KPU-RISC/KPU/Eagle/3. Instruction Decoder/04_ALU.brd

## EAGLE design Eagle/3. Instruction Decoder/04_ALU.brd (2017-04-16)

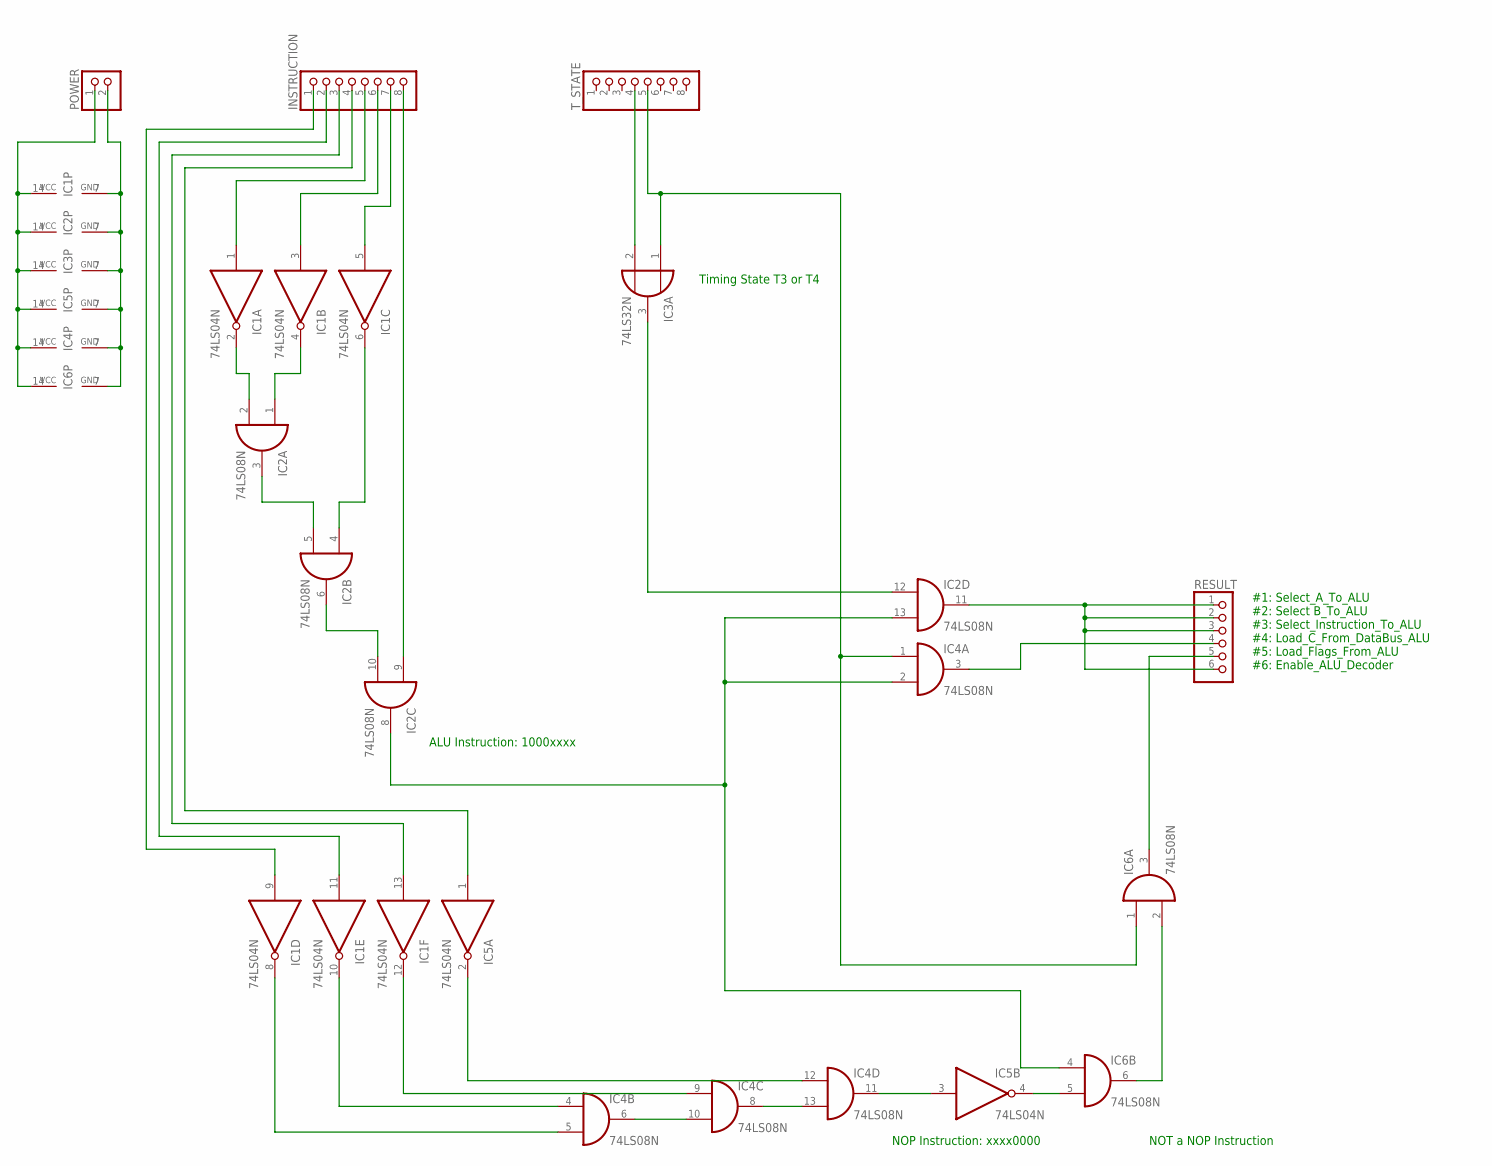
[picture p17: schematic 04_ALU.sch]

Parts:
IC1, IC5: 74LS04N; DIL14
IC2, IC4, IC6: 74LS08N; DIL14
IC3: 74LS32N; DIL14
INSTRUCTION: PINHD-1X8; 1X08
POWER: PINHD-1X2; 1X02
RESULT: PINHD-1X6; 1X06
T_STATE: PINHD-1X8; 1X08

Connections:
GND: IC1.7 (GND), IC2.7 (GND), IC3.7 (GND), IC4.7 (GND), IC5.7 (GND), IC6.7 (GND), POWER.2
unnamed: IC1.1 (I), INSTRUCTION.5
unnamed: IC1.3 (I), INSTRUCTION.6
unnamed: IC1.5 (I), INSTRUCTION.7
unnamed: IC1.2 (O), IC2.2 (I1)
unnamed: IC1.4 (O), IC2.1 (I0)
unnamed: IC2.3 (O), IC2.5 (I1)
unnamed: IC1.6 (O), IC2.4 (I0)
unnamed: IC2.9 (I0), INSTRUCTION.8
unnamed: IC2.6 (O), IC2.10 (I1)
unnamed: IC3.2 (I1), T_STATE.4
unnamed: IC3.1 (I0), IC4.1 (I0), IC6.1 (I0), T_STATE.5
unnamed: IC2.8 (O), IC2.13 (I1), IC4.2 (I1), IC6.4 (I0)
unnamed: IC2.12 (I0), IC3.3 (O)
unnamed: IC2.11 (O), RESULT.1, RESULT.2, RESULT.3, RESULT.6
unnamed: IC4.3 (O), RESULT.4
unnamed: IC1.9 (I), INSTRUCTION.1
unnamed: IC1.11 (I), INSTRUCTION.2
unnamed: IC1.13 (I), INSTRUCTION.3
unnamed: IC5.1 (I), INSTRUCTION.4
unnamed: IC1.8 (O), IC4.5 (I1)
unnamed: IC1.10 (O), IC4.4 (I0)
unnamed: IC4.6 (O), IC4.10 (I1)
unnamed: IC1.12 (O), IC4.9 (I0)
unnamed: IC4.8 (O), IC4.13 (I1)
unnamed: IC4.12 (I0), IC5.2 (O)
unnamed: IC4.11 (O), IC5.3 (I)
unnamed: IC5.4 (O), IC6.5 (I1)
unnamed: IC6.3 (O), RESULT.5
unnamed: IC6.2 (I1), IC6.6 (O)
VCC: IC1.14 (VCC), IC2.14 (VCC), IC3.14 (VCC), IC4.14 (VCC), IC5.14 (VCC), IC6.14 (VCC), POWER.1

Notes on the sheet:
ALU Instruction: 1000xxxx
Timing State T3 or T4
#1: Select_A_To_ALU #2: Select B_To_ALU #3: Select_Instruction_To_ALU #4: Load_C_From_DataBus_ALU #5: Load_Flags_From_ALU #6: Enable_ALU_Decoder
NOP Instruction: xxxx0000
NOT a NOP Instruction

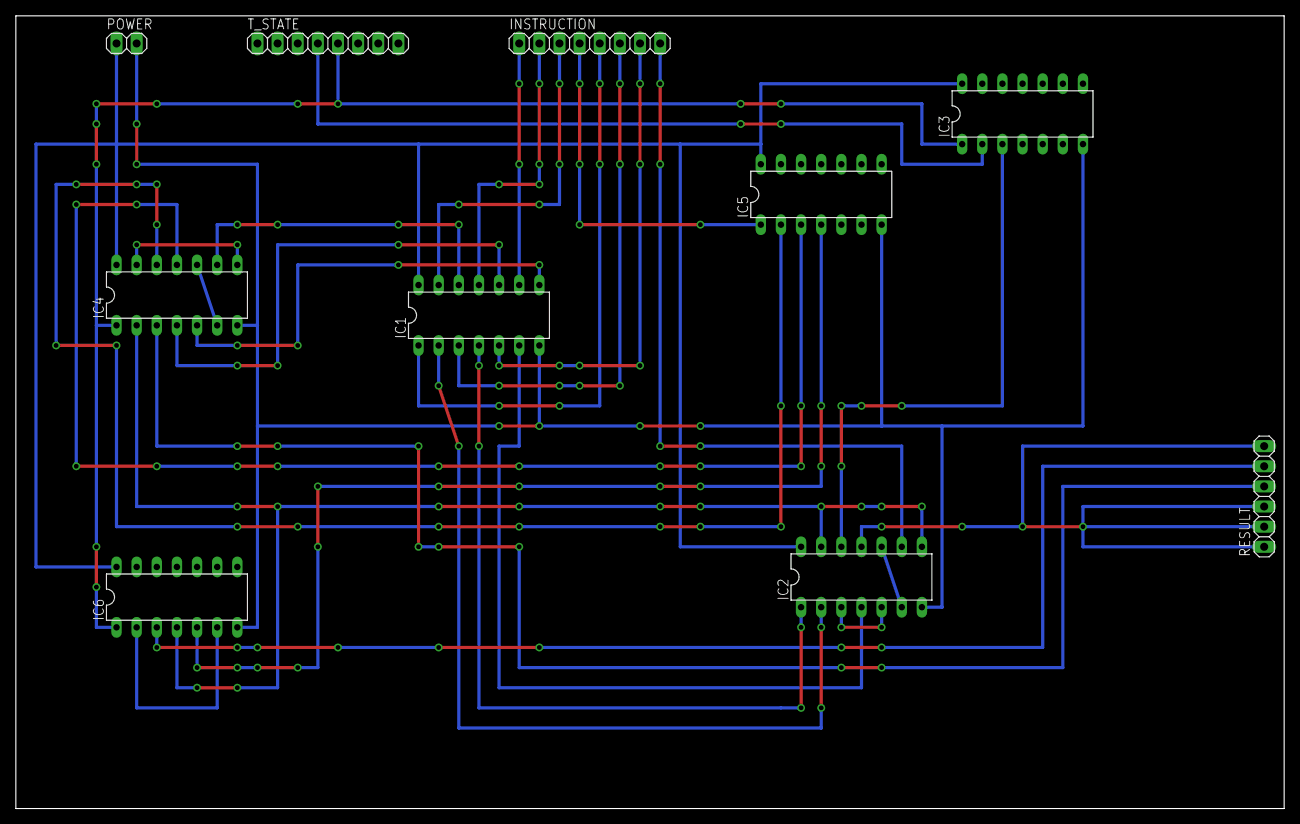
[picture p18: board 04_ALU.brd from above]

Board: 2 copper layers, 160.0 x 100.0 mm, 10 parts (0 on the bottom side), 31 nets.
