KPU-RISC/KPU/Eagle/3. Instruction Decoder/13_RESTOREFLAGS.brd

## EAGLE design Eagle/3. Instruction Decoder/13_RESTOREFLAGS.brd (2017-04-16)

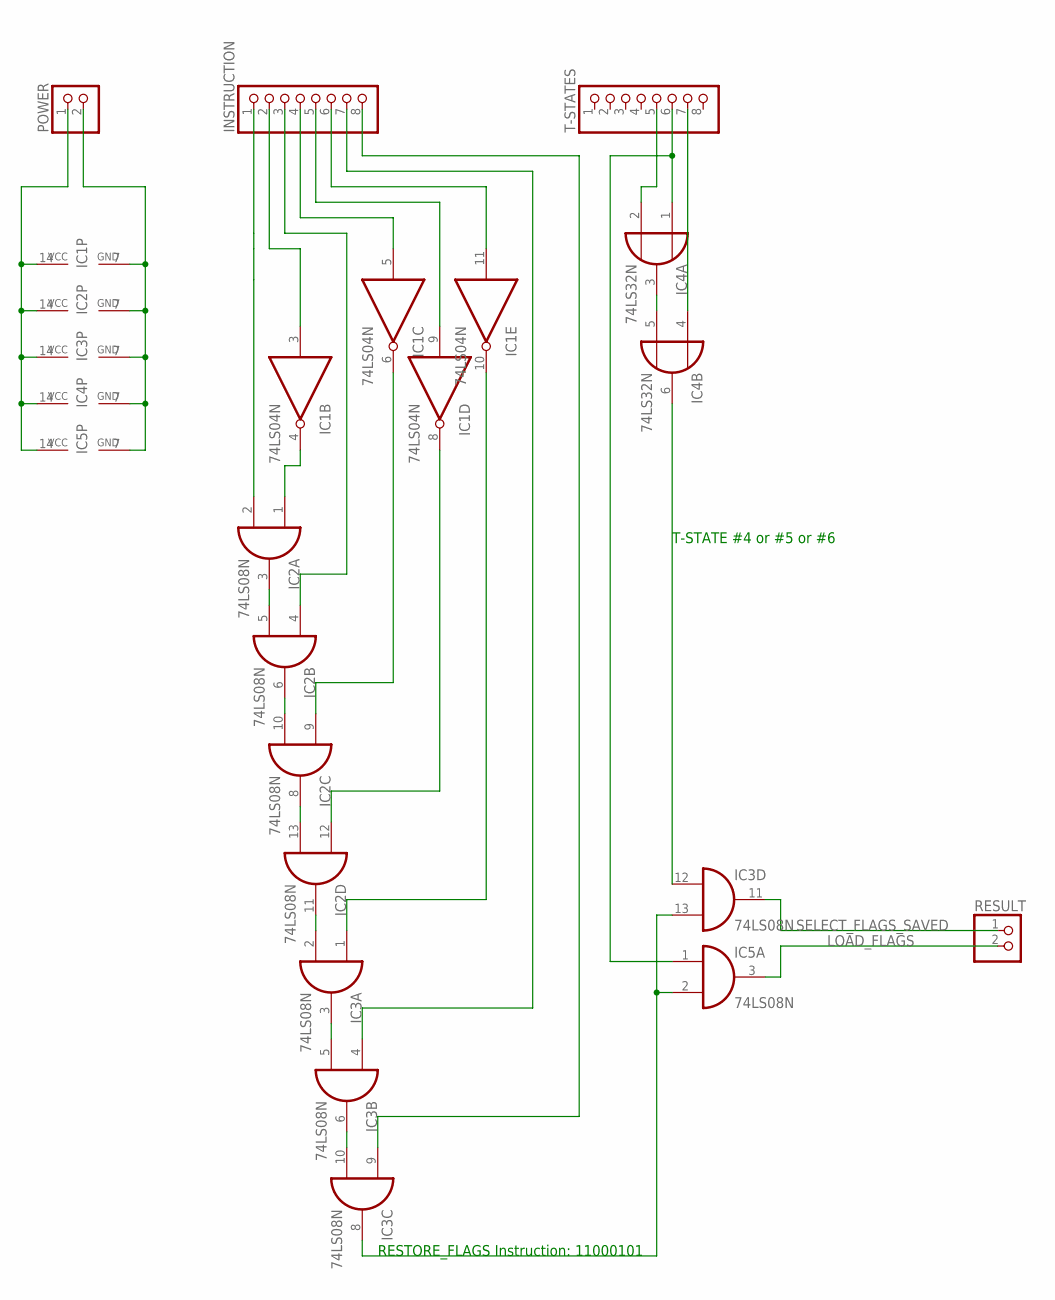
[picture p19: schematic 13_RESTOREFLAGS.sch]

Parts:
IC1: 74LS04N; DIL14
IC2, IC3, IC5: 74LS08N; DIL14
IC4: 74LS32N; DIL14
INSTRUCTION: PINHD-1X8; 1X08
POWER: PINHD-1X2; 1X02
RESULT: PINHD-1X2; 1X02
T-STATES: PINHD-1X8; 1X08

Connections:
GND: IC1.7 (GND), IC2.7 (GND), IC3.7 (GND), IC4.7 (GND), IC5.7 (GND), POWER.2
LOAD_FLAGS: IC5.3 (O), RESULT.2
unnamed: IC2.2 (I1), INSTRUCTION.1
unnamed: IC1.3 (I), INSTRUCTION.2
unnamed: IC2.4 (I0), INSTRUCTION.3
unnamed: IC4.3 (O), IC4.5 (I1)
unnamed: IC1.4 (O), IC2.1 (I0)
unnamed: IC1.6 (O), IC2.9 (I0)
unnamed: IC1.8 (O), IC2.12 (I0)
unnamed: IC1.10 (O), IC3.1 (I0)
unnamed: IC1.5 (I), INSTRUCTION.4
unnamed: IC1.9 (I), INSTRUCTION.5
unnamed: IC1.11 (I), INSTRUCTION.6
unnamed: IC3.4 (I0), INSTRUCTION.7
unnamed: IC3.9 (I0), INSTRUCTION.8
unnamed: IC4.4 (I0), T-STATES.7
unnamed: IC2.3 (O), IC2.5 (I1)
unnamed: IC2.6 (O), IC2.10 (I1)
unnamed: IC2.8 (O), IC2.13 (I1)
unnamed: IC2.11 (O), IC3.2 (I1)
unnamed: IC3.3 (O), IC3.5 (I1)
unnamed: IC3.6 (O), IC3.10 (I1)
unnamed: IC3.8 (O), IC3.13 (I1), IC5.2 (I1)
unnamed: IC4.1 (I0), IC5.1 (I0), T-STATES.6
unnamed: IC3.12 (I0), IC4.6 (O)
unnamed: IC4.2 (I1), T-STATES.5
SELECT_FLAGS_SAVED: IC3.11 (O), RESULT.1
VCC: IC1.14 (VCC), IC2.14 (VCC), IC3.14 (VCC), IC4.14 (VCC), IC5.14 (VCC), POWER.1

Notes on the sheet:
RESTORE_FLAGS Instruction: 11000101
T-STATE #4 or #5 or #6

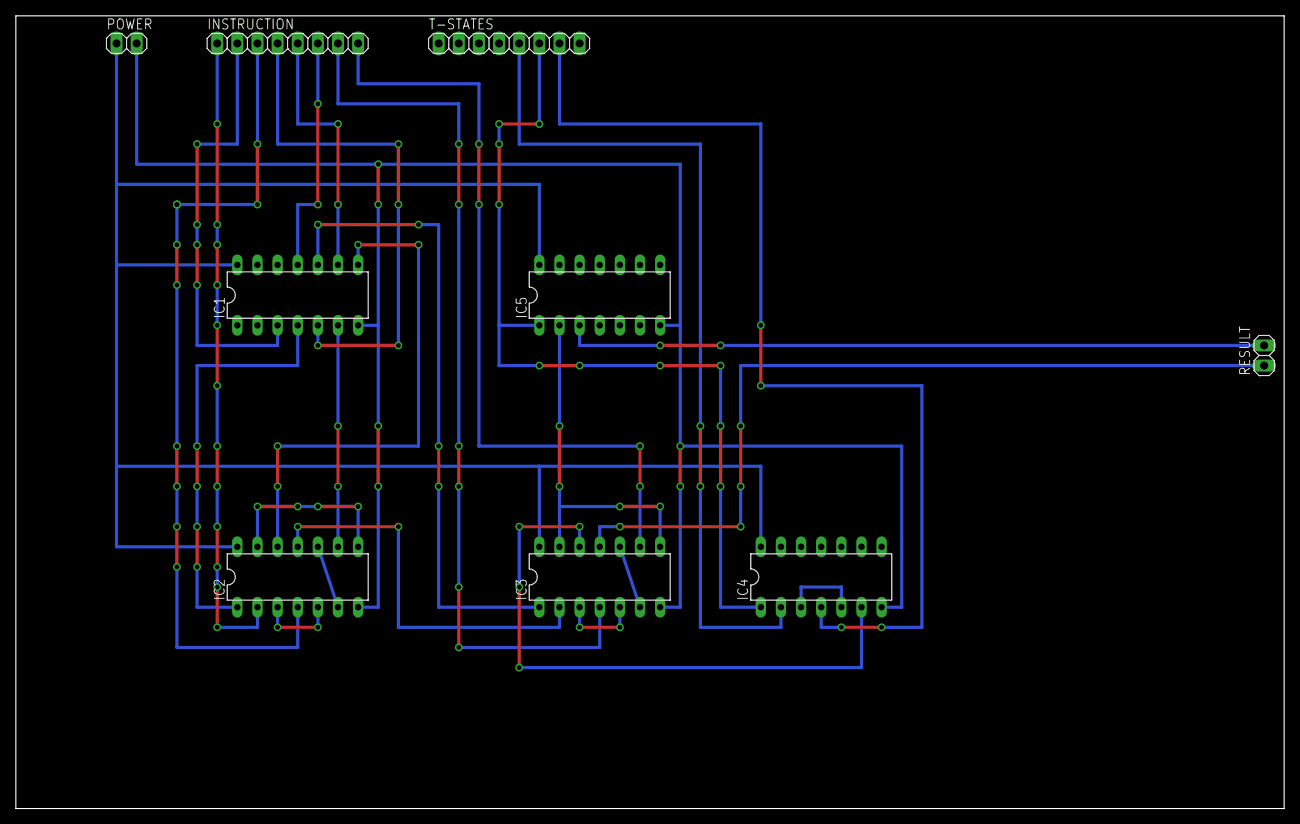
[picture p20: board 13_RESTOREFLAGS.brd from above]

Board: 2 copper layers, 160.0 x 100.0 mm, 9 parts (0 on the bottom side), 28 nets.
