KPU-RISC/KPU/Eagle/1. General/ControlLineSelector.brd

## EAGLE design Eagle/1. General/ControlLineSelector.brd (2017-04-16)

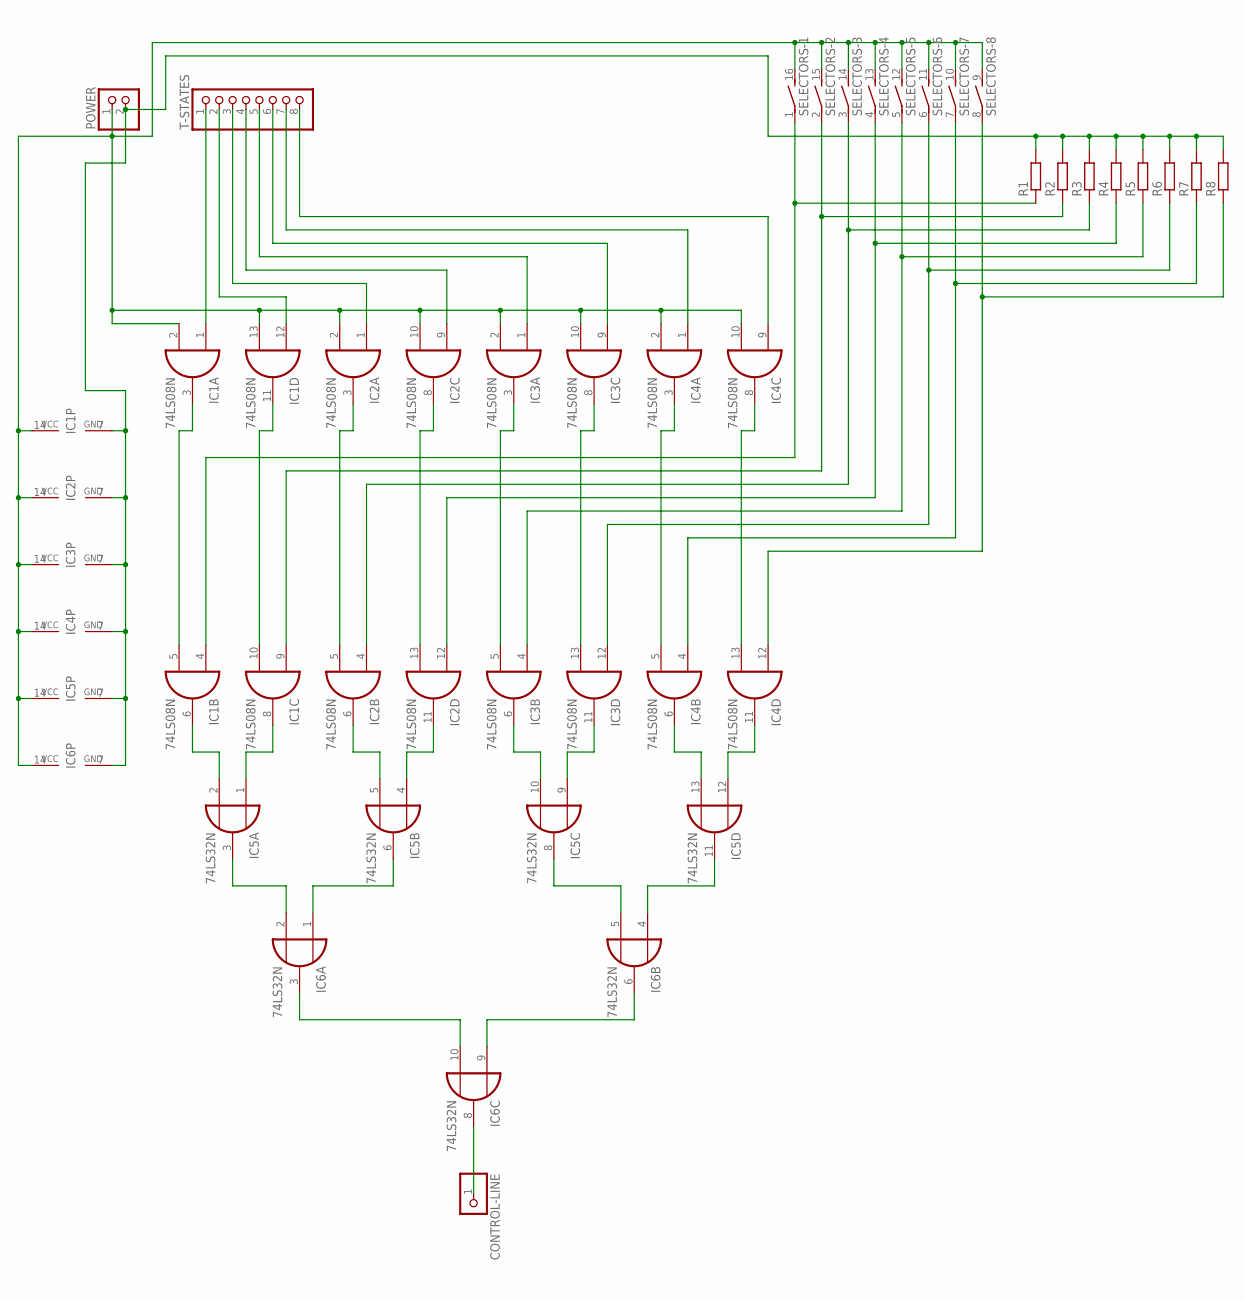
[picture p21: schematic ControlLineSelector.sch]

Parts:
CONTROL-LINE: PINHD-1X1; 1X01
IC1, IC2, IC3, IC4: 74LS08N; DIL14
IC5, IC6: 74LS32N; DIL14
POWER: PINHD-1X2; 1X02
R1, R2, R3, R4, R5, R6, R7, R8: R-EU_0207/7; 0207/7
SELECTORS: DIP08S
T-STATES: PINHD-1X8; 1X08

Connections:
GND: IC1.7 (GND), IC2.7 (GND), IC3.7 (GND), IC4.7 (GND), IC5.7 (GND), IC6.7 (GND), POWER.2, R1.2, R2.2, R3.2, R4.2, R5.2, R6.2, R7.2, R8.2
unnamed: IC1.3 (O), IC1.5 (I1)
unnamed: IC1.1 (I0), T-STATES.1
unnamed: IC1.4 (I0), R1.1, SELECTORS.1
unnamed: IC1.12 (I0), T-STATES.2
unnamed: IC4.1 (I0), T-STATES.7
unnamed: IC1.10 (I1), IC1.11 (O)
unnamed: IC1.9 (I0), R2.1, SELECTORS.2 (1)
unnamed: IC4.9 (I0), T-STATES.8
unnamed: IC2.3 (O), IC2.5 (I1)
unnamed: IC2.8 (O), IC2.13 (I1)
unnamed: IC3.3 (O), IC3.5 (I1)
unnamed: IC2.1 (I0), T-STATES.3
unnamed: IC2.9 (I0), T-STATES.4
unnamed: IC3.1 (I0), T-STATES.5
unnamed: IC3.9 (I0), T-STATES.6
unnamed: IC3.8 (O), IC3.13 (I1)
unnamed: IC4.3 (O), IC4.5 (I1)
unnamed: IC4.8 (O), IC4.13 (I1)
unnamed: IC2.4 (I0), R3.1, SELECTORS.3 (1)
unnamed: IC3.4 (I0), R5.1, SELECTORS.5 (1)
unnamed: IC3.12 (I0), R6.1, SELECTORS.6 (1)
unnamed: IC4.4 (I0), R7.1, SELECTORS.7 (1)
unnamed: IC4.12 (I0), R8.1, SELECTORS.8 (1)
unnamed: IC1.6 (O), IC5.2 (I1)
unnamed: IC1.8 (O), IC5.1 (I0)
unnamed: IC2.6 (O), IC5.5 (I1)
unnamed: IC2.11 (O), IC5.4 (I0)
unnamed: IC3.6 (O), IC5.10 (I1)
unnamed: IC3.11 (O), IC5.9 (I0)
unnamed: IC4.6 (O), IC5.13 (I1)
unnamed: IC4.11 (O), IC5.12 (I0)
unnamed: IC5.3 (O), IC6.2 (I1)
unnamed: IC5.6 (O), IC6.1 (I0)
unnamed: IC5.8 (O), IC6.5 (I1)
unnamed: IC5.11 (O), IC6.4 (I0)
unnamed: IC6.3 (O), IC6.10 (I1)
unnamed: IC6.6 (O), IC6.9 (I0)
unnamed: CONTROL-LINE.1, IC6.8 (O)
unnamed: IC2.12 (I0), R4.1, SELECTORS.4 (1)
VCC: IC1.2 (I1), IC1.13 (I1), IC1.14 (VCC), IC2.2 (I1), IC2.10 (I1), IC2.14 (VCC), IC3.2 (I1), IC3.10 (I1), IC3.14 (VCC), IC4.2 (I1), IC4.10 (I1), IC4.14 (VCC), IC5.14 (VCC), IC6.14 (VCC), POWER.1, SELECTORS.9 (2), SELECTORS.10 (2), SELECTORS.11 (2), SELECTORS.12 (2), SELECTORS.13 (2), SELECTORS.14 (2), SELECTORS.15 (2), SELECTORS.16 (2)

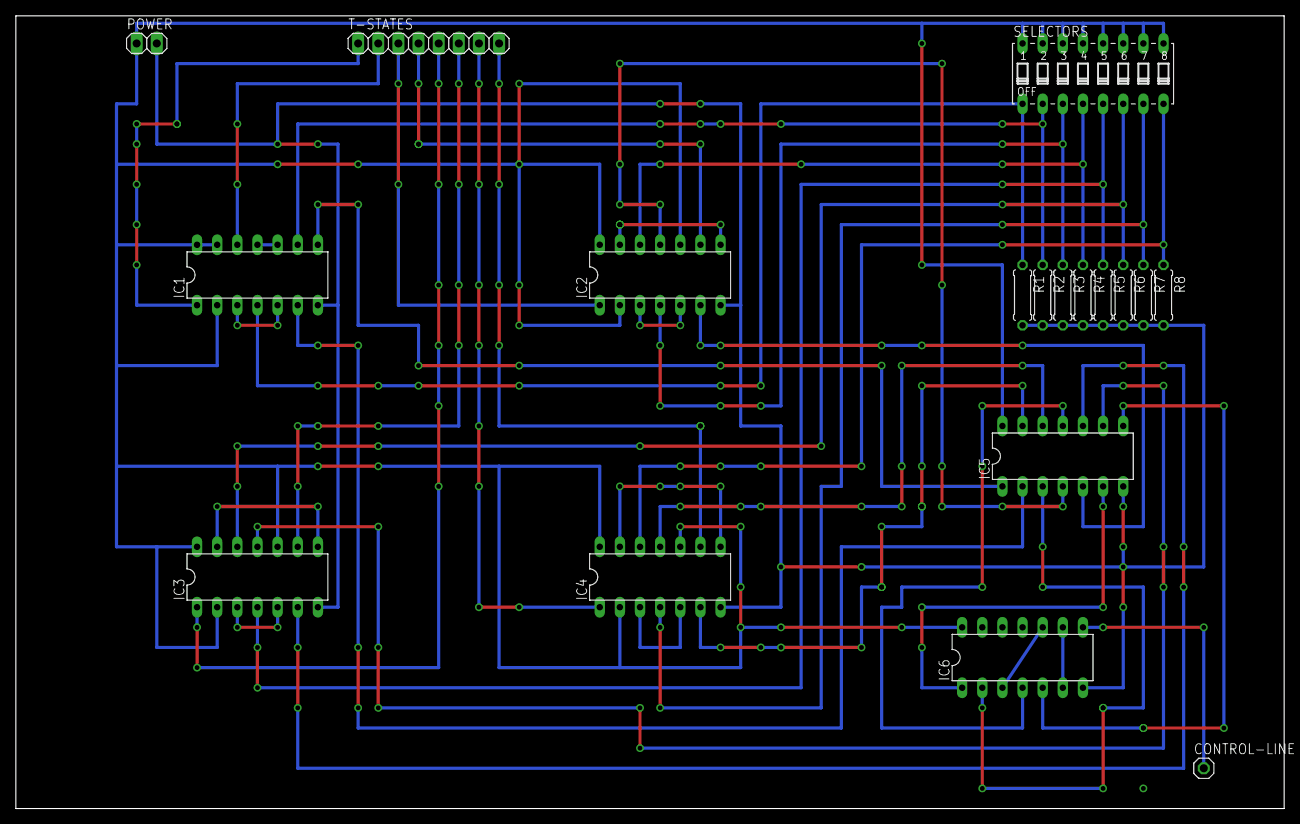
[picture p22: board ControlLineSelector.brd from above]

Board: 2 copper layers, 160.0 x 100.0 mm, 18 parts (0 on the bottom side), 41 nets.
