KPU-RISC/KPU/Eagle/1. General/64K SRAM Memory Controller.brd

## EAGLE design Eagle/1. General/64K SRAM Memory Controller.brd (2017-04-16)

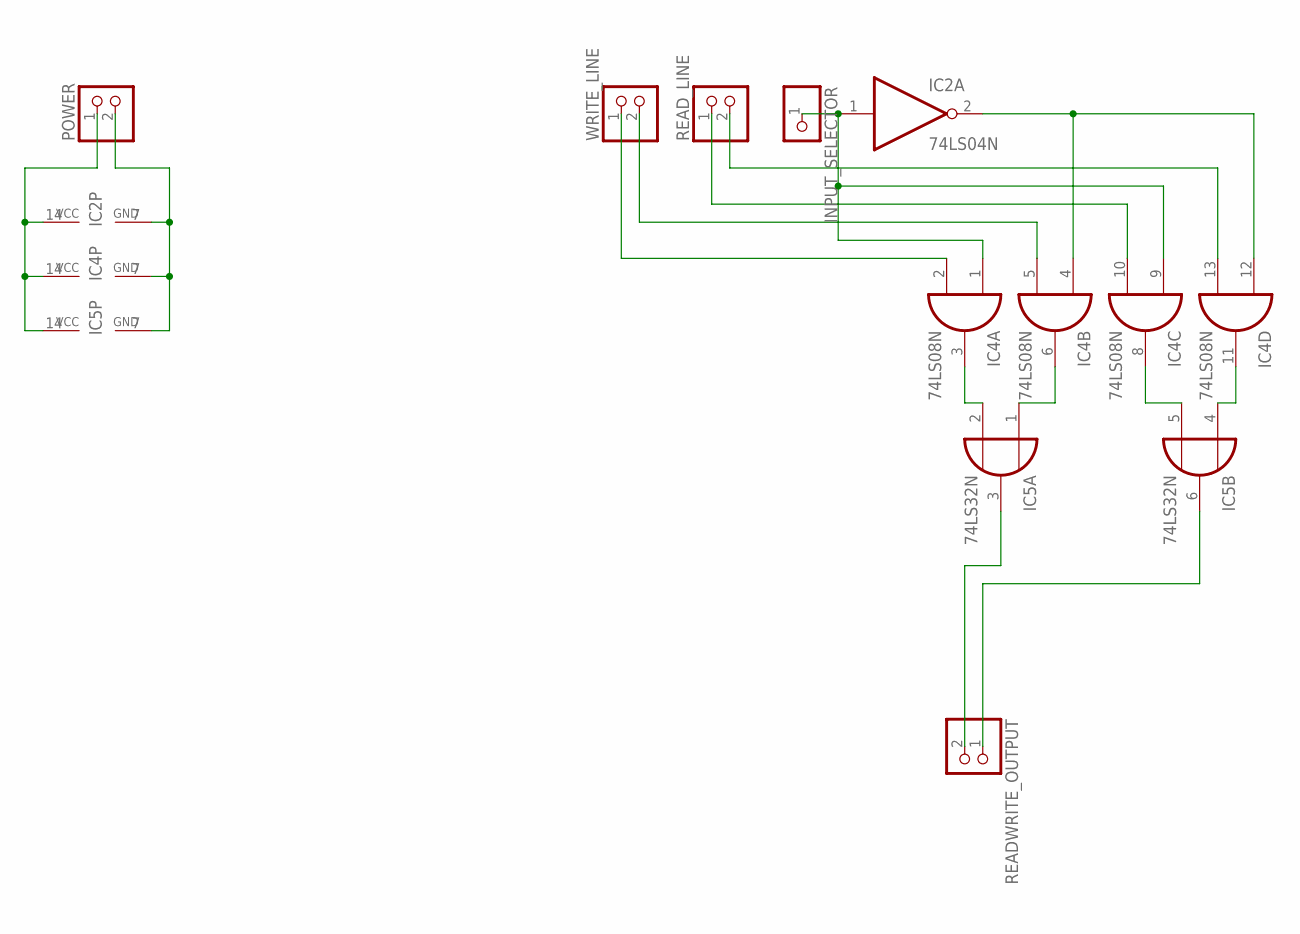
[picture p23: schematic 64K SRAM Memory Controller.sch]

Parts:
IC2: 74LS04N; DIL14
IC4: 74LS08N; DIL14
IC5: 74LS32N; DIL14
INPUT_SELECTOR: PINHD-1X1; 1X01
POWER: PINHD-1X2; 1X02
READWRITE_OUTPUT: PINHD-1X2; 1X02
READ_LINE: PINHD-1X2; 1X02
WRITE_LINE: PINHD-1X2; 1X02

Connections:
GND: IC2.7 (GND), IC4.7 (GND), IC5.7 (GND), POWER.2
unnamed: IC2.1 (I), IC4.1 (I0), IC4.9 (I0), INPUT_SELECTOR.1
unnamed: IC5.6 (O), READWRITE_OUTPUT.1
unnamed: IC4.2 (I1), WRITE_LINE.1
unnamed: IC4.5 (I1), WRITE_LINE.2
unnamed: IC2.2 (O), IC4.4 (I0), IC4.12 (I0)
unnamed: IC5.3 (O), READWRITE_OUTPUT.2
unnamed: IC4.10 (I1), READ_LINE.1
unnamed: IC4.13 (I1), READ_LINE.2
unnamed: IC4.3 (O), IC5.2 (I1)
unnamed: IC4.6 (O), IC5.1 (I0)
unnamed: IC4.8 (O), IC5.5 (I1)
unnamed: IC4.11 (O), IC5.4 (I0)
VCC: IC2.14 (VCC), IC4.14 (VCC), IC5.14 (VCC), POWER.1

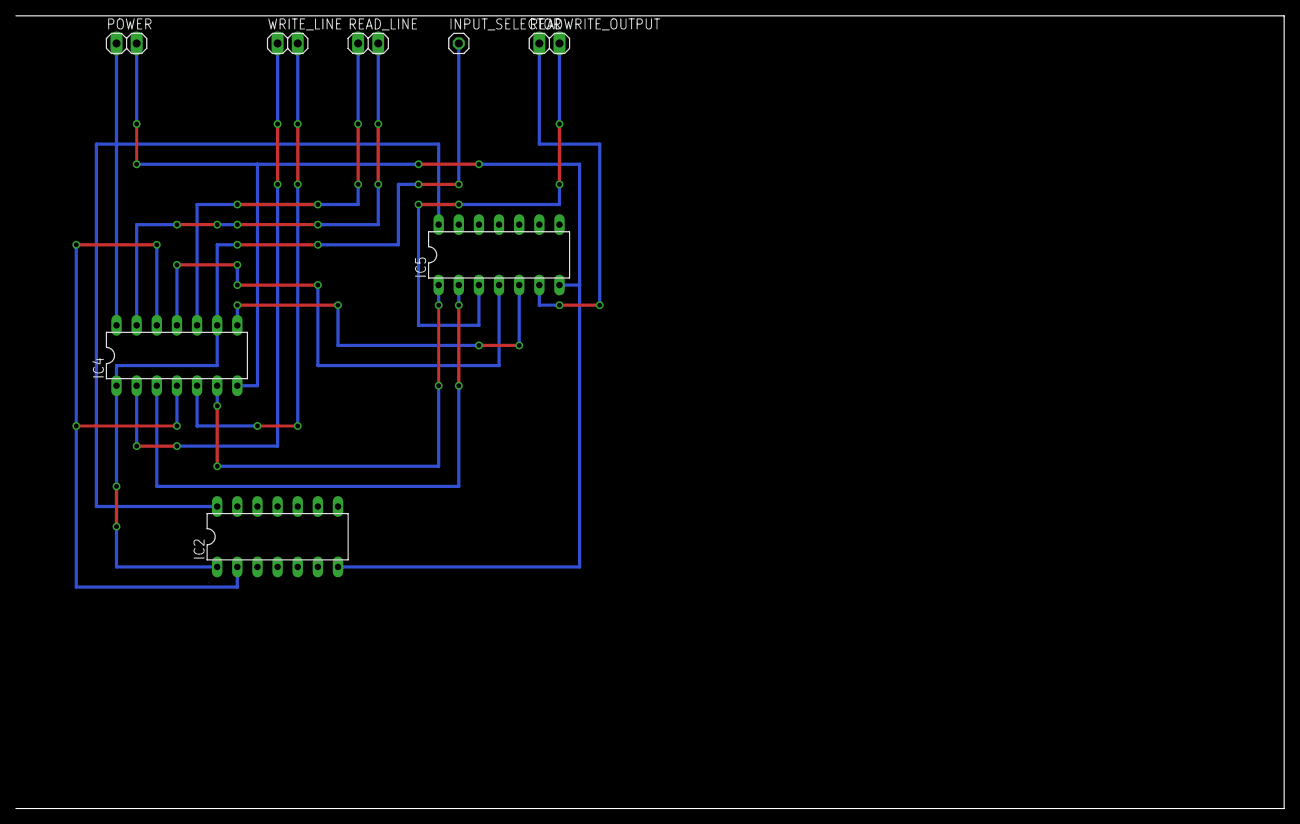
[picture p24: board 64K SRAM Memory Controller.brd from above]

Board: 2 copper layers, 160.0 x 100.0 mm, 8 parts (0 on the bottom side), 14 nets.
