KPU-RISC/KPU/Eagle/1. General/Clock Circuit.brd

## EAGLE design Eagle/1. General/Clock Circuit.brd (2017-04-16)

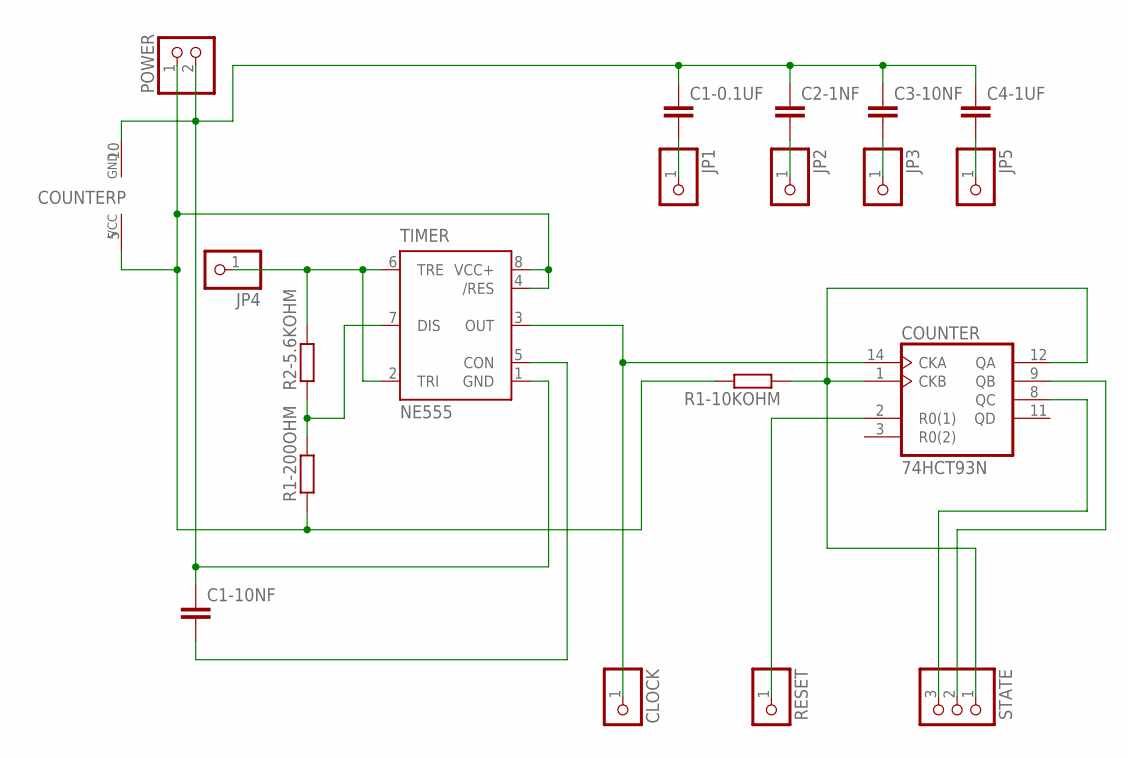
[picture p25: schematic Clock Circuit.sch]

Parts:
C1-0.1UF, C1-10NF, C2-1NF, C3-10NF, C4-1UF: C-EU050-025X075; C050-025X075
CLOCK: PINHD-1X1; 1X01
COUNTER: 74HCT93N; DIL14
JP1, JP2, JP3, JP4, JP5: PINHD-1X1; 1X01
POWER: PINHD-1X2; 1X02
R1-10KOHM, R1-200OHM, R2-5.6KOHM: R-EU_0207/10; 0207/10
RESET: PINHD-1X1; 1X01
STATE: PINHD-1X3; 1X03
TIMER: NE555; DIL-08

Connections:
GND: C1-0.1UF.1, C1-10NF.1, C2-1NF.1, C3-10NF.1, C4-1UF.1, COUNTER.10 (GND), POWER.2, TIMER.1 (GND)
unnamed: CLOCK.1, COUNTER.14 (CKA), TIMER.3 (OUT)
unnamed: JP4.1, R2-5.6KOHM.2, TIMER.2 (TRI), TIMER.6 (TRE)
unnamed: COUNTER.1 (CKB), COUNTER.12 (QA), R1-10KOHM.1, STATE.1
unnamed: COUNTER.2 (R0(1)), RESET.1
unnamed: COUNTER.8 (QC), STATE.3
unnamed: COUNTER.9 (QB), STATE.2
unnamed: C1-10NF.2, TIMER.5 (CON)
unnamed: C1-0.1UF.2, JP1.1
unnamed: C2-1NF.2, JP2.1
unnamed: C3-10NF.2, JP3.1
unnamed: C4-1UF.2, JP5.1
unnamed: R1-200OHM.2, R2-5.6KOHM.1, TIMER.7 (DIS)
VCC: COUNTER.5 (VCC), POWER.1, R1-10KOHM.2, R1-200OHM.1, TIMER.4 (/RES), TIMER.8 (VCC+)

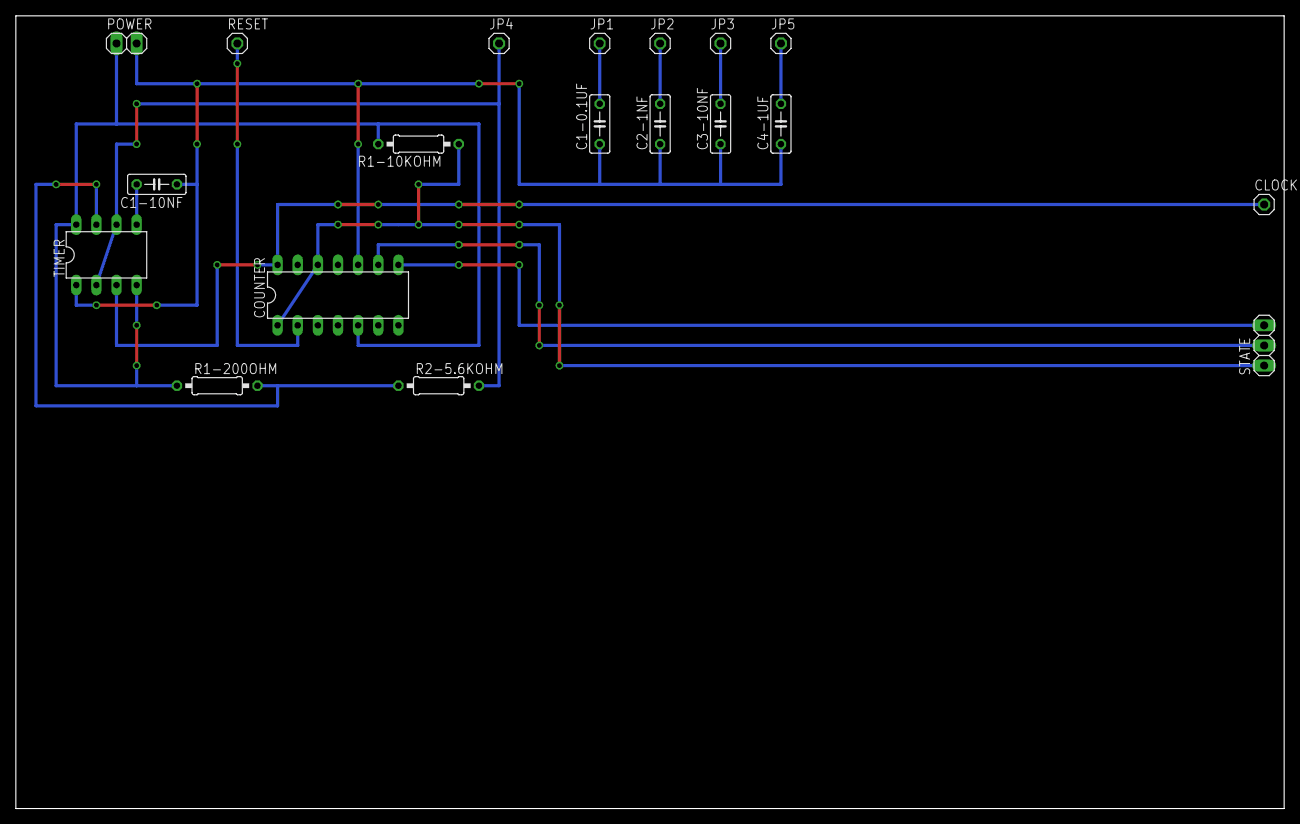
[picture p26: board Clock Circuit.brd from above]

Board: 2 copper layers, 160.0 x 100.0 mm, 19 parts (0 on the bottom side), 14 nets.
