KPU-RISC/KPU/Eagle/3. Instruction Decoder/03_HLT.brd

## EAGLE design Eagle/3. Instruction Decoder/03_HLT.brd (2017-04-16)

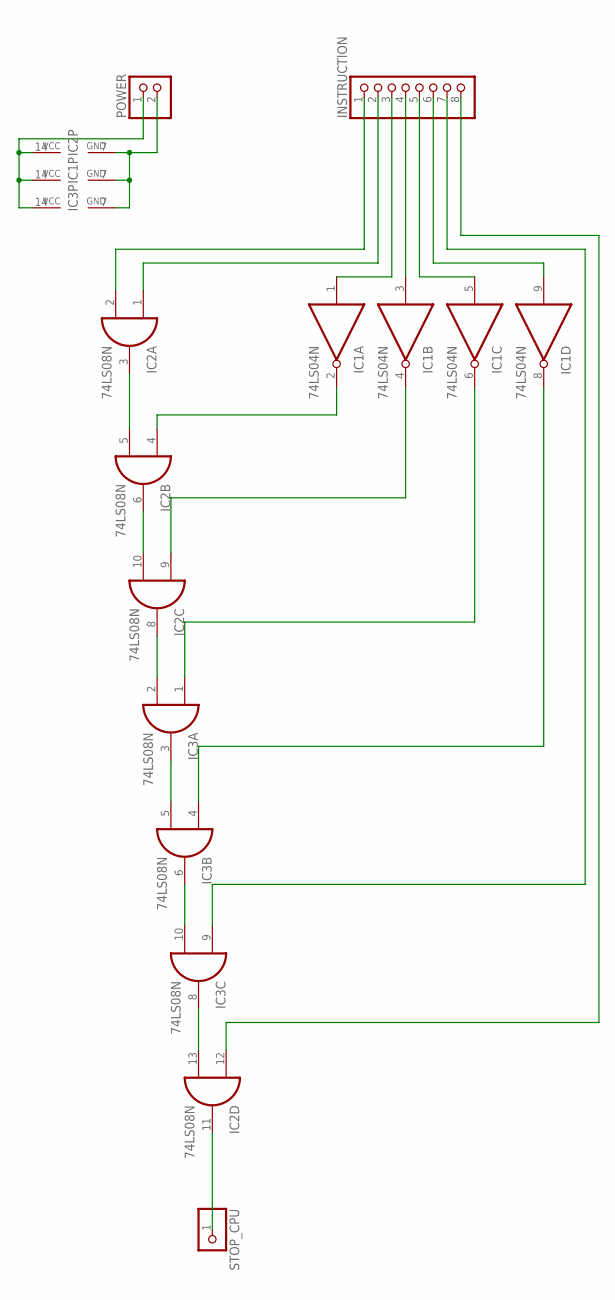
[picture p27: schematic 03_HLT.sch]

Parts:
IC1: 74LS04N; DIL14
IC2, IC3: 74LS08N; DIL14
INSTRUCTION: PINHD-1X8; 1X08
POWER: PINHD-1X2; 1X02
STOP_CPU: PINHD-1X1; 1X01

Connections:
GND: IC1.7 (GND), IC2.7 (GND), IC3.7 (GND), POWER.2
unnamed: IC1.1 (I), INSTRUCTION.3
unnamed: IC1.3 (I), INSTRUCTION.4
unnamed: IC1.5 (I), INSTRUCTION.5
unnamed: IC1.9 (I), INSTRUCTION.6
unnamed: IC2.2 (I1), INSTRUCTION.1
unnamed: IC2.1 (I0), INSTRUCTION.2
unnamed: IC2.3 (O), IC2.5 (I1)
unnamed: IC1.2 (O), IC2.4 (I0)
unnamed: IC2.6 (O), IC2.10 (I1)
unnamed: IC1.4 (O), IC2.9 (I0)
unnamed: IC2.8 (O), IC3.2 (I1)
unnamed: IC1.6 (O), IC3.1 (I0)
unnamed: IC3.3 (O), IC3.5 (I1)
unnamed: IC1.8 (O), IC3.4 (I0)
unnamed: IC3.6 (O), IC3.10 (I1)
unnamed: IC3.9 (I0), INSTRUCTION.7
unnamed: IC2.13 (I1), IC3.8 (O)
unnamed: IC2.12 (I0), INSTRUCTION.8
unnamed: IC2.11 (O), STOP_CPU.1
VCC: IC1.14 (VCC), IC2.14 (VCC), IC3.14 (VCC), POWER.1

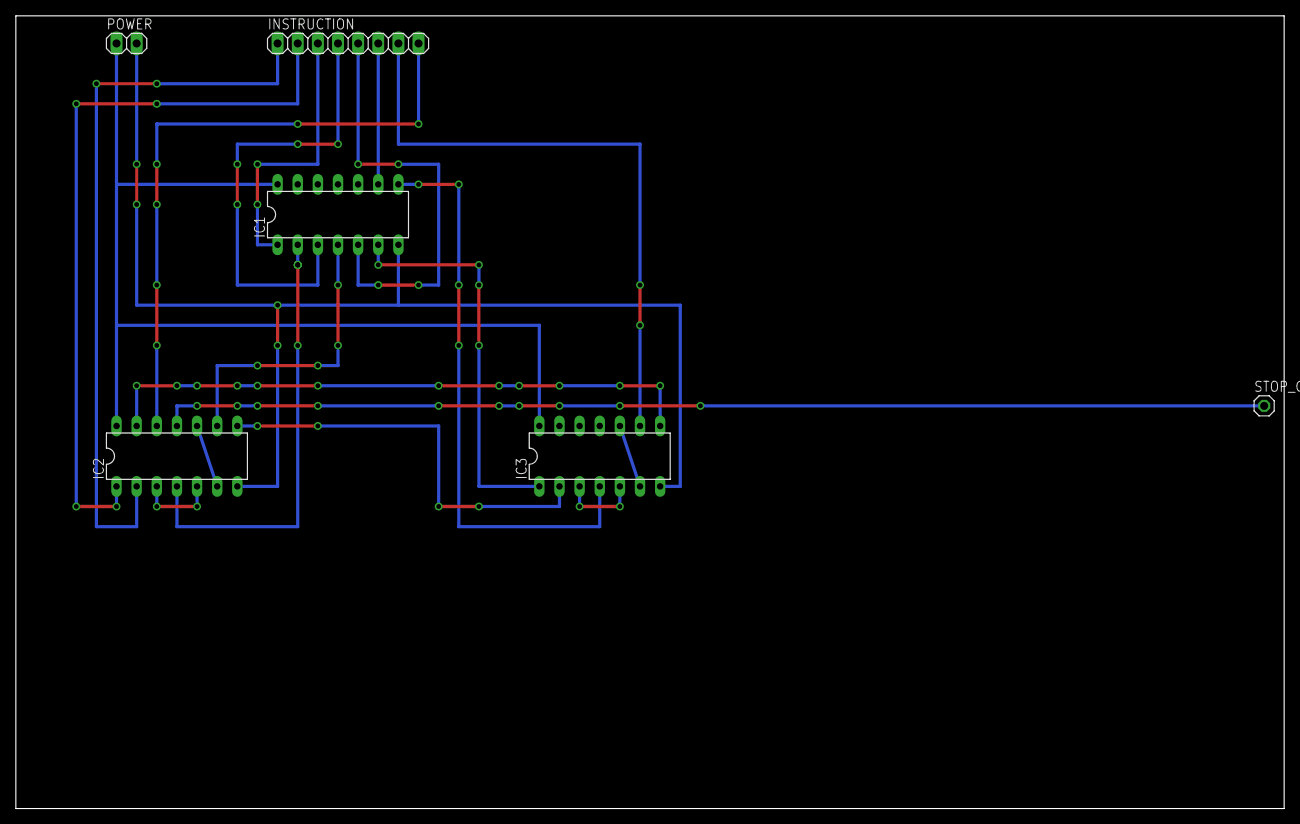
[picture p28: board 03_HLT.brd from above]

Board: 2 copper layers, 160.0 x 100.0 mm, 6 parts (0 on the bottom side), 21 nets.
