KPU-RISC/KPU/Eagle/2. ALU/04_ADD.brd

## EAGLE design Eagle/2. ALU/04_ADD.brd (2017-04-16)

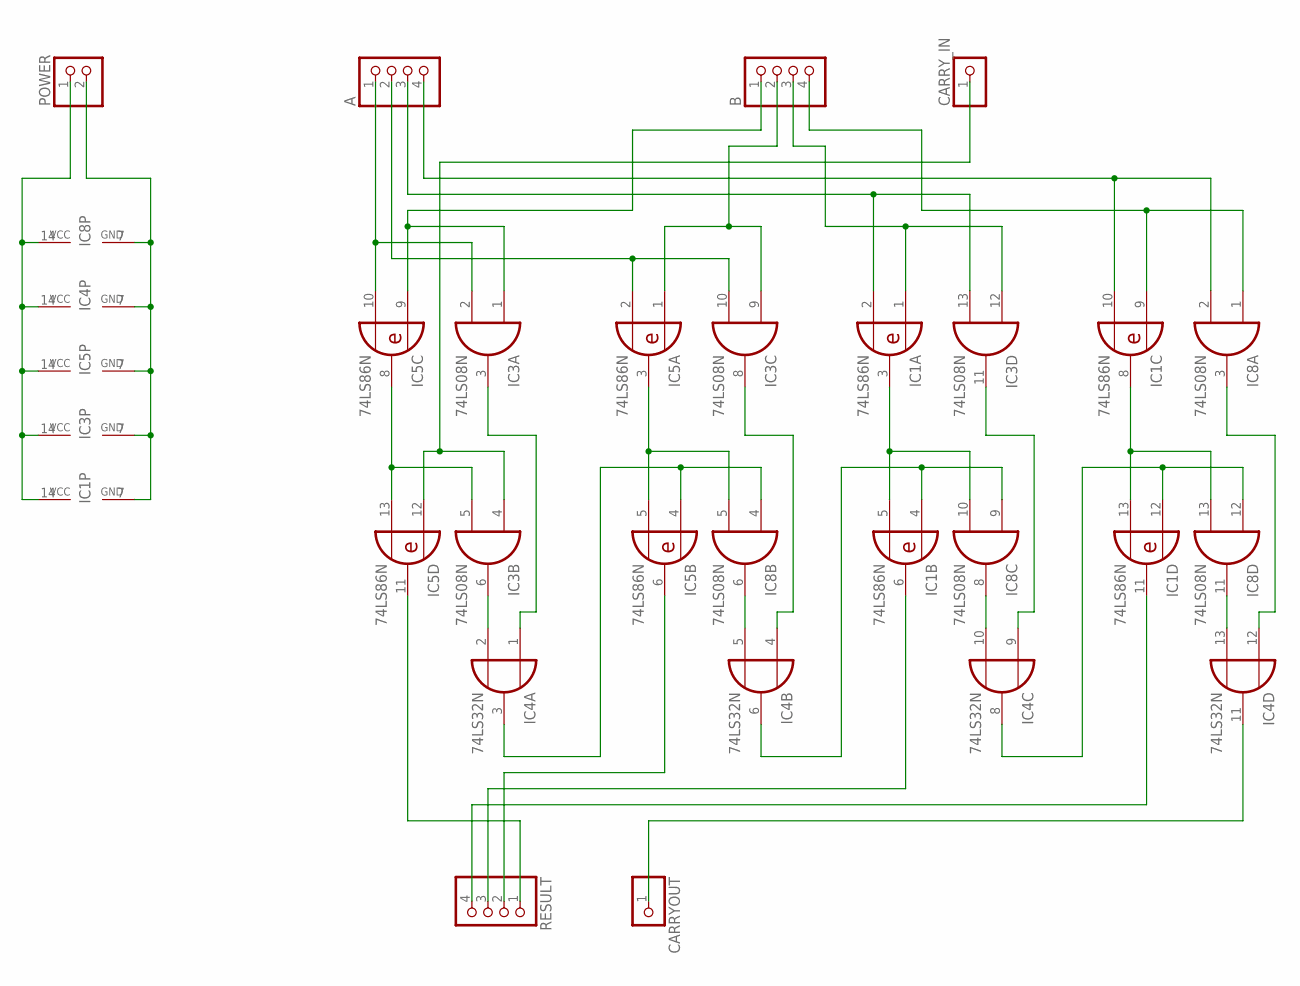
[picture p29: schematic 04_ADD.sch]

Parts:
A: PINHD-1X4; 1X04
B: PINHD-1X4; 1X04
CARRYOUT: PINHD-1X1; 1X01
CARRY_IN: PINHD-1X1; 1X01
IC1, IC5: 74LS86N; DIL14
IC3, IC8: 74LS08N; DIL14
IC4: 74LS32N; DIL14
POWER: PINHD-1X2; 1X02
RESULT: PINHD-1X4; 1X04

Connections:
CARRY_OUT: CARRYOUT.1, IC4.11 (O)
GND: IC1.7 (GND), IC3.7 (GND), IC4.7 (GND), IC5.7 (GND), IC8.7 (GND), POWER.2
unnamed: B.1, IC3.1 (I0), IC5.9 (I0)
unnamed: B.3, IC1.1 (I0), IC3.12 (I0)
unnamed: CARRY_IN.1, IC3.4 (I0), IC5.12 (I0)
unnamed: A.1, IC3.2 (I1), IC5.10 (I1)
unnamed: IC3.5 (I1), IC5.8 (O), IC5.13 (I1)
unnamed: IC5.11 (O), RESULT.1
unnamed: IC3.3 (O), IC4.1 (I0)
unnamed: IC3.6 (O), IC4.2 (I1)
unnamed: A.2, IC3.10 (I1), IC5.2 (I1)
unnamed: A.3, IC1.2 (I1), IC3.13 (I1)
unnamed: A.4, IC1.10 (I1), IC8.2 (I1)
unnamed: B.2, IC3.9 (I0), IC5.1 (I0)
unnamed: B.4, IC1.9 (I0), IC8.1 (I0)
unnamed: IC5.3 (O), IC5.5 (I1), IC8.5 (I1)
unnamed: IC1.6 (O), RESULT.3
unnamed: IC1.3 (O), IC1.5 (I1), IC8.10 (I1)
unnamed: IC1.8 (O), IC1.13 (I1), IC8.13 (I1)
unnamed: IC4.3 (O), IC5.4 (I0), IC8.4 (I0)
unnamed: IC5.6 (O), RESULT.2
unnamed: IC1.11 (O), RESULT.4
unnamed: IC4.5 (I1), IC8.6 (O)
unnamed: IC4.10 (I1), IC8.8 (O)
unnamed: IC4.13 (I1), IC8.11 (O)
unnamed: IC3.8 (O), IC4.4 (I0)
unnamed: IC3.11 (O), IC4.9 (I0)
unnamed: IC4.12 (I0), IC8.3 (O)
unnamed: IC1.4 (I0), IC4.6 (O), IC8.9 (I0)
unnamed: IC1.12 (I0), IC4.8 (O), IC8.12 (I0)
VCC: IC1.14 (VCC), IC3.14 (VCC), IC4.14 (VCC), IC5.14 (VCC), IC8.14 (VCC), POWER.1

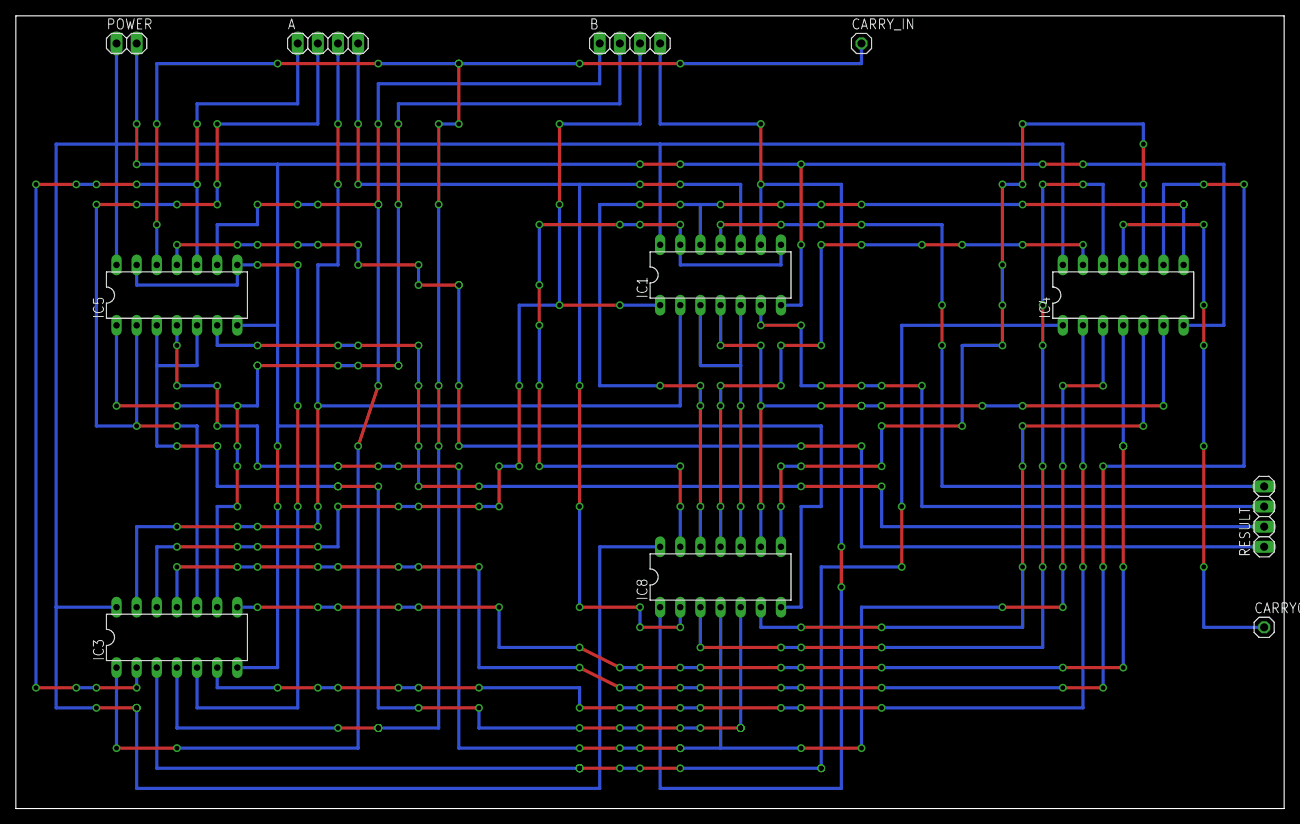
[picture p30: board 04_ADD.brd from above]

Board: 2 copper layers, 160.0 x 100.0 mm, 11 parts (0 on the bottom side), 31 nets.
