KPU-RISC/KPU/Eagle/1. General/CPU_Stop.brd

## EAGLE design Eagle/1. General/CPU_Stop.brd (2017-04-16)

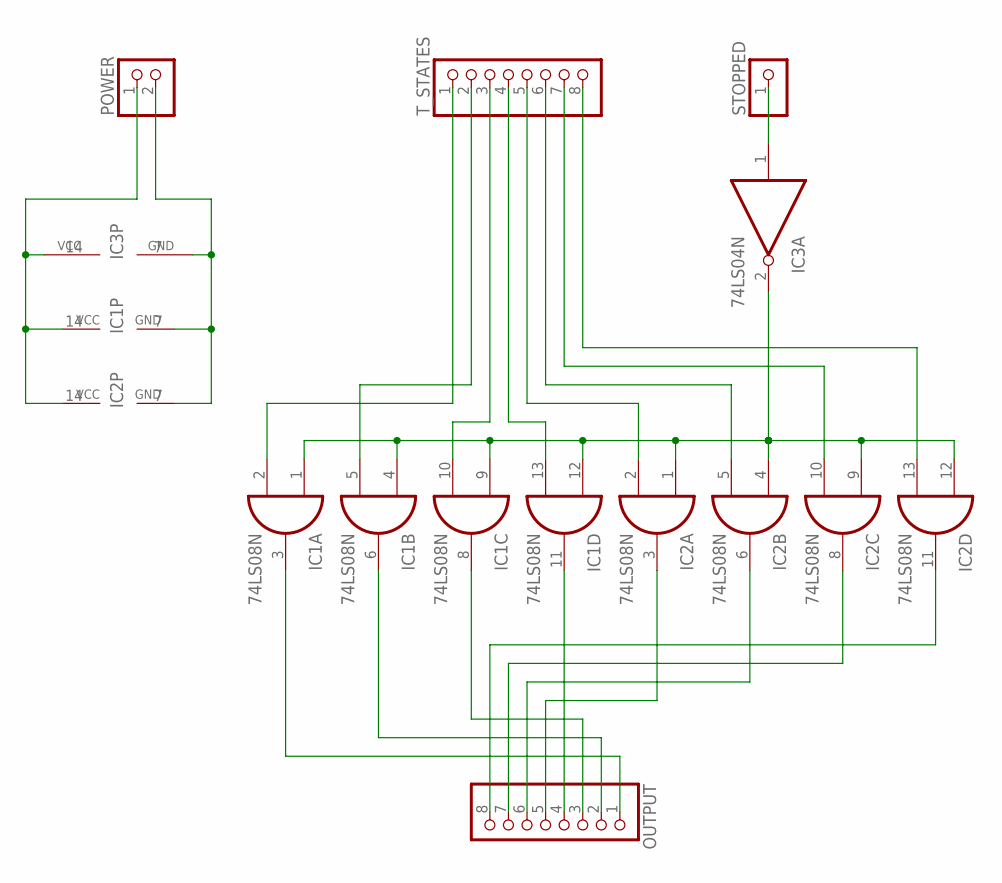
[picture p31: schematic CPU_Stop.sch]

Parts:
IC1, IC2: 74LS08N; DIL14
IC3: 74LS04N; DIL14
OUTPUT: PINHD-1X8; 1X08
POWER: PINHD-1X2; 1X02
STOPPED: PINHD-1X1; 1X01
T_STATES: PINHD-1X8; 1X08

Connections:
GND: IC1.7 (GND), IC2.7 (GND), IC3.7 (GND), POWER.2
unnamed: IC3.1 (I), STOPPED.1
unnamed: IC1.1 (I0), IC1.4 (I0), IC1.9 (I0), IC1.12 (I0), IC2.1 (I0), IC2.4 (I0), IC2.9 (I0), IC2.12 (I0), IC3.2 (O)
unnamed: IC1.2 (I1), T_STATES.1
unnamed: IC1.5 (I1), T_STATES.2
unnamed: IC1.10 (I1), T_STATES.3
unnamed: IC1.13 (I1), T_STATES.4
unnamed: IC2.2 (I1), T_STATES.5
unnamed: IC2.5 (I1), T_STATES.6
unnamed: IC2.10 (I1), T_STATES.7
unnamed: IC2.13 (I1), T_STATES.8
unnamed: IC1.3 (O), OUTPUT.1
unnamed: IC1.6 (O), OUTPUT.2
unnamed: IC1.8 (O), OUTPUT.3
unnamed: IC1.11 (O), OUTPUT.4
unnamed: IC2.3 (O), OUTPUT.5
unnamed: IC2.6 (O), OUTPUT.6
unnamed: IC2.8 (O), OUTPUT.7
unnamed: IC2.11 (O), OUTPUT.8
VCC: IC1.14 (VCC), IC2.14 (VCC), IC3.14 (VCC), POWER.1

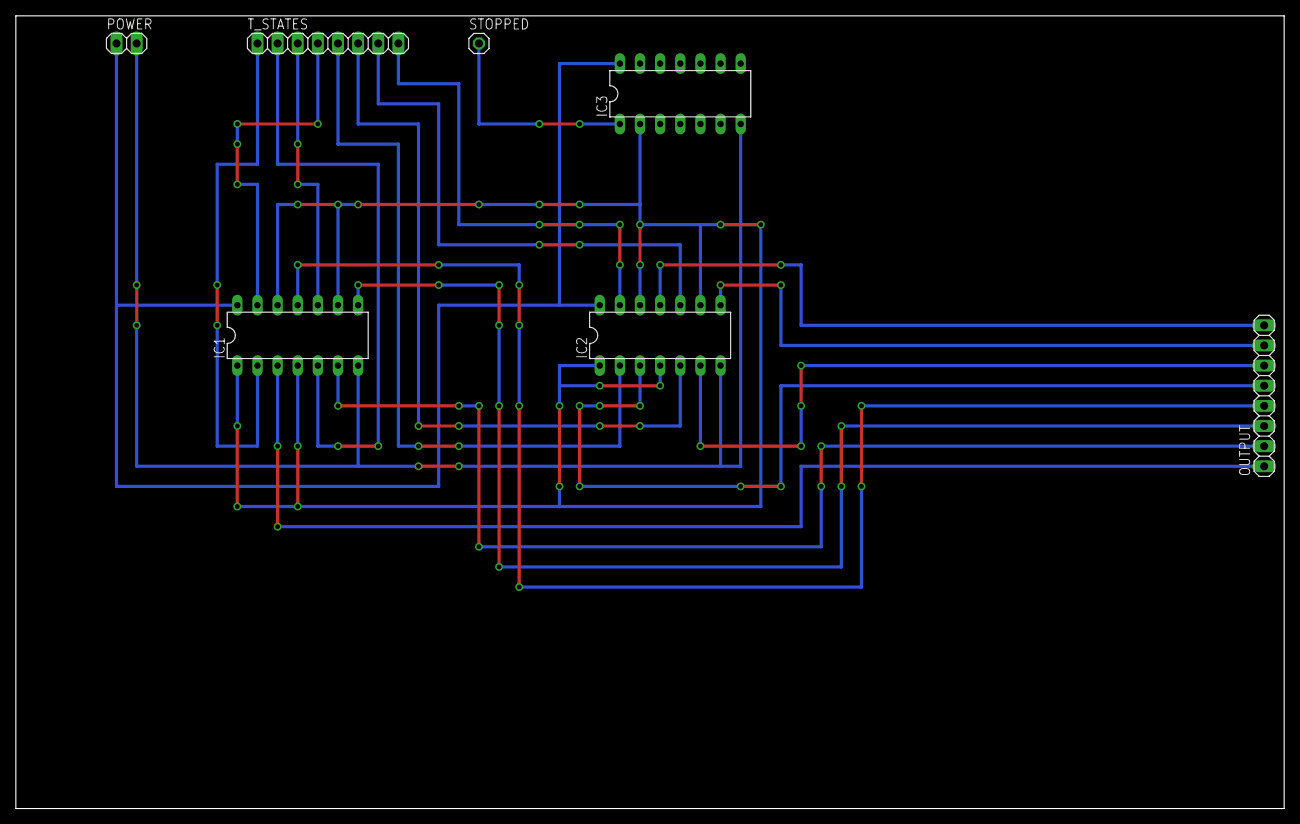
[picture p32: board CPU_Stop.brd from above]

Board: 2 copper layers, 160.0 x 100.0 mm, 7 parts (0 on the bottom side), 20 nets.
