KPU-RISC/KPU/Eagle/3. Instruction Decoder/05_ALU_OUT.brd

## EAGLE design Eagle/3. Instruction Decoder/05_ALU_OUT.brd (2017-04-16)

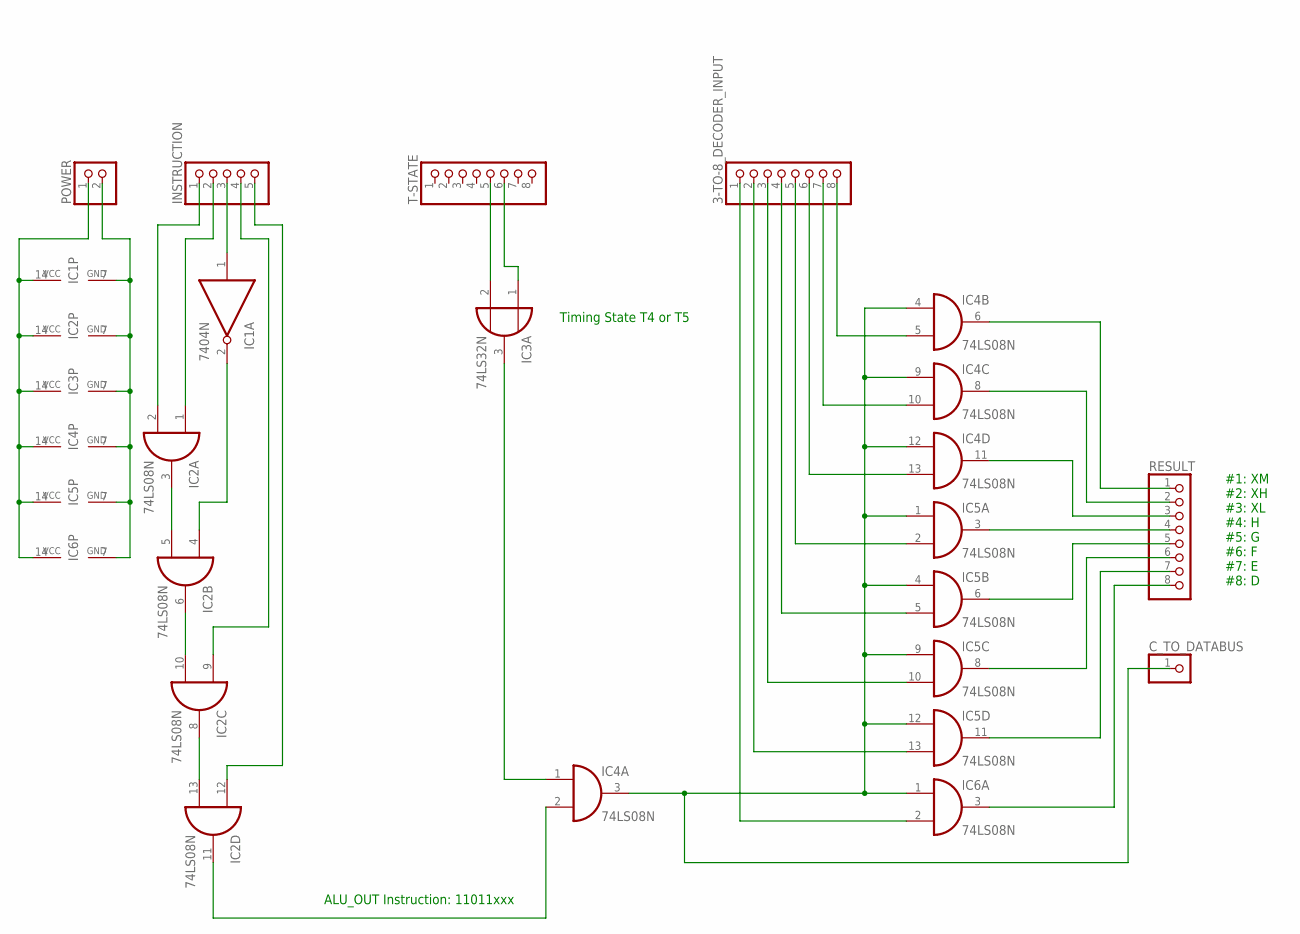
[picture p33: schematic 05_ALU_OUT.sch]

Parts:
3-TO-8_DECODER_INPUT: PINHD-1X8; 1X08
C_TO_DATABUS: PINHD-1X1; 1X01
IC1: 7404N; DIL14
IC2, IC4, IC5, IC6: 74LS08N; DIL14
IC3: 74LS32N; DIL14
INSTRUCTION: PINHD-1X5; 1X05
POWER: PINHD-1X2; 1X02
RESULT: PINHD-1X8; 1X08
T-STATE: PINHD-1X8; 1X08

Connections:
GND: IC1.7 (GND), IC2.7 (GND), IC3.7 (GND), IC4.7 (GND), IC5.7 (GND), IC6.7 (GND), POWER.2
unnamed: IC1.1 (I), INSTRUCTION.3
unnamed: IC2.2 (I1), INSTRUCTION.1
unnamed: IC2.1 (I0), INSTRUCTION.2
unnamed: IC2.3 (O), IC2.5 (I1)
unnamed: IC1.2 (O), IC2.4 (I0)
unnamed: IC2.6 (O), IC2.10 (I1)
unnamed: IC2.9 (I0), INSTRUCTION.4
unnamed: IC2.8 (O), IC2.13 (I1)
unnamed: IC2.12 (I0), INSTRUCTION.5
unnamed: IC2.11 (O), IC4.2 (I1)
unnamed: IC3.2 (I1), T-STATE.5
unnamed: IC3.1 (I0), T-STATE.6
unnamed: IC3.3 (O), IC4.1 (I0)
unnamed: C_TO_DATABUS.1, IC4.3 (O), IC4.4 (I0), IC4.9 (I0), IC4.12 (I0), IC5.1 (I0), IC5.4 (I0), IC5.9 (I0), IC5.12 (I0), IC6.1 (I0)
unnamed: 3-TO-8_DECODER_INPUT.8, IC4.5 (I1)
unnamed: 3-TO-8_DECODER_INPUT.7, IC4.10 (I1)
unnamed: 3-TO-8_DECODER_INPUT.6, IC4.13 (I1)
unnamed: 3-TO-8_DECODER_INPUT.5, IC5.2 (I1)
unnamed: 3-TO-8_DECODER_INPUT.4, IC5.5 (I1)
unnamed: 3-TO-8_DECODER_INPUT.3, IC5.10 (I1)
unnamed: 3-TO-8_DECODER_INPUT.2, IC5.13 (I1)
unnamed: 3-TO-8_DECODER_INPUT.1, IC6.2 (I1)
unnamed: IC4.6 (O), RESULT.1
unnamed: IC4.8 (O), RESULT.2
unnamed: IC4.11 (O), RESULT.3
unnamed: IC5.3 (O), RESULT.4
unnamed: IC5.6 (O), RESULT.5
unnamed: IC5.8 (O), RESULT.6
unnamed: IC5.11 (O), RESULT.7
unnamed: IC6.3 (O), RESULT.8
VCC: IC1.14 (VCC), IC2.14 (VCC), IC3.14 (VCC), IC4.14 (VCC), IC5.14 (VCC), IC6.14 (VCC), POWER.1

Notes on the sheet:
ALU_OUT Instruction: 11011xxx
Timing State T4 or T5
#1: XM #2: XH #3: XL #4: H #5: G #6: F #7: E #8: D

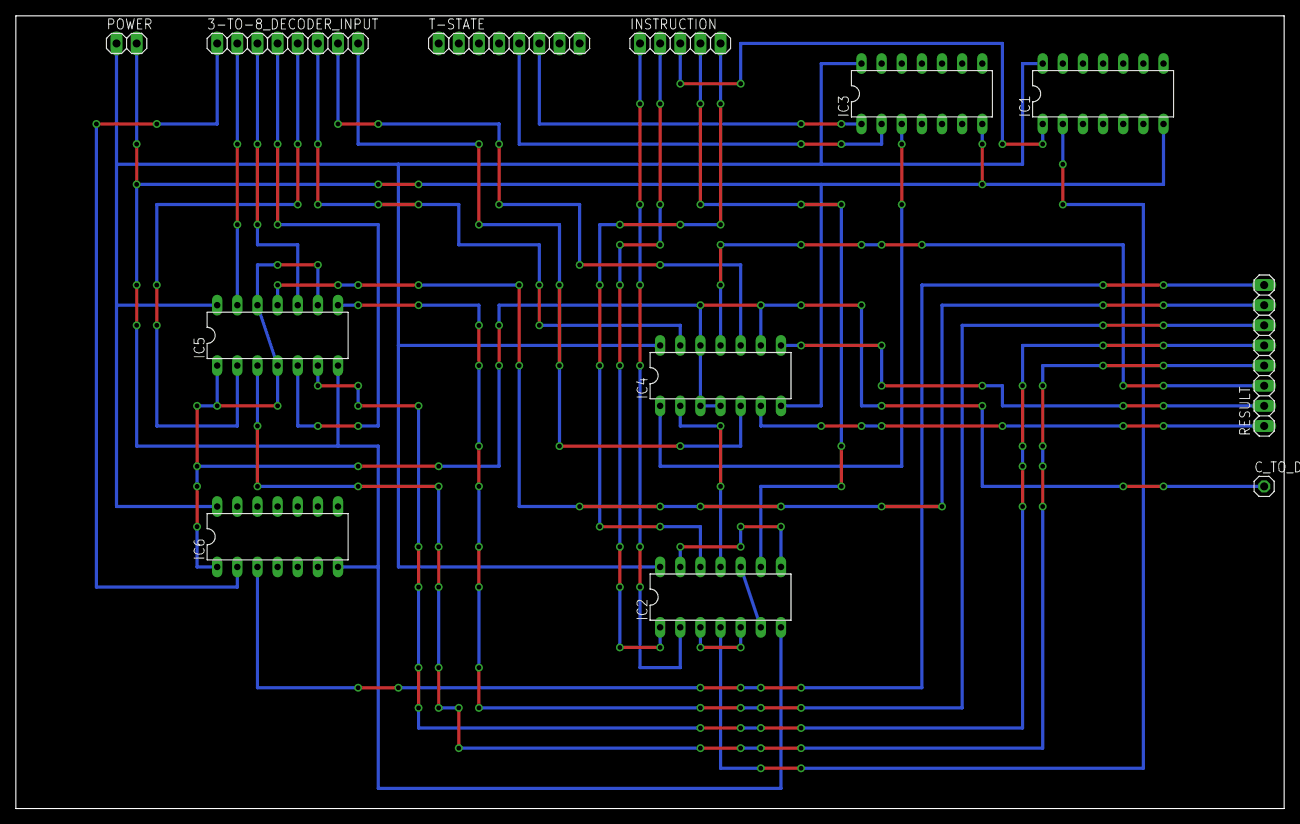
[picture p34: board 05_ALU_OUT.brd from above]

Board: 2 copper layers, 160.0 x 100.0 mm, 12 parts (0 on the bottom side), 32 nets.
