KPU-RISC/KPU/Eagle/1. General/3-to-8 Decoder.brd

## EAGLE design Eagle/1. General/3-to-8 Decoder.brd (2017-04-16)

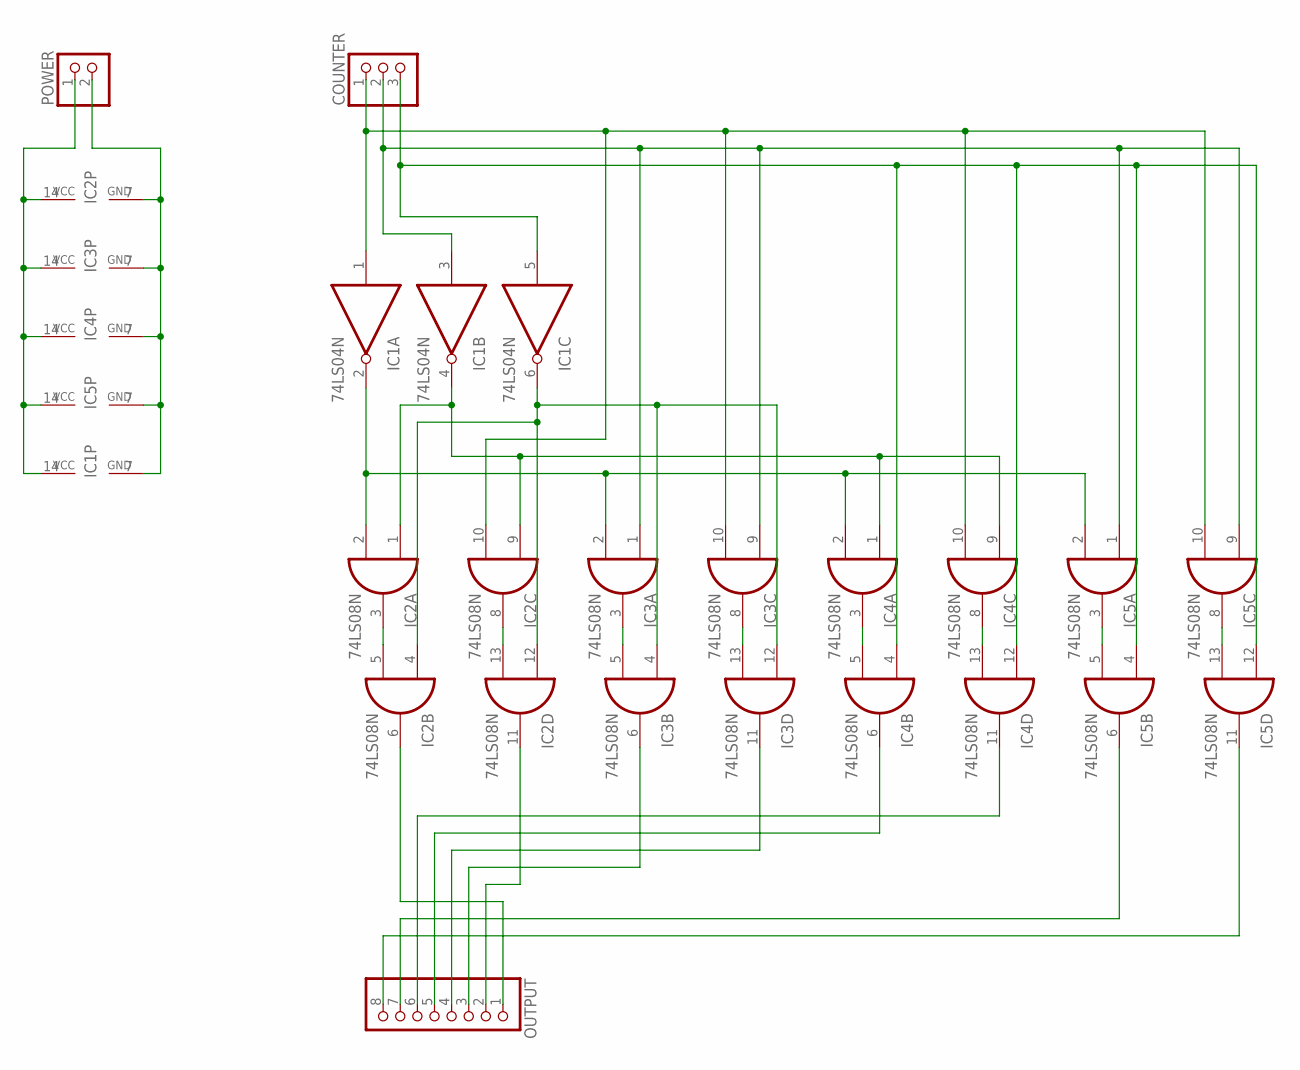
[picture p35: schematic 3-to-8 Decoder.sch]

Parts:
COUNTER: PINHD-1X3; 1X03
IC1: 74LS04N; DIL14
IC2, IC3, IC4, IC5: 74LS08N; DIL14
OUTPUT: PINHD-1X8; 1X08
POWER: PINHD-1X2; 1X02

Connections:
GND: IC1.7 (GND), IC2.7 (GND), IC3.7 (GND), IC4.7 (GND), IC5.7 (GND), POWER.2
unnamed: COUNTER.1, IC1.1 (I), IC2.10 (I1), IC3.10 (I1), IC4.10 (I1), IC5.10 (I1)
unnamed: COUNTER.2, IC1.3 (I), IC3.1 (I0), IC3.9 (I0), IC5.1 (I0), IC5.9 (I0)
unnamed: COUNTER.3, IC1.5 (I), IC4.4 (I0), IC4.12 (I0), IC5.4 (I0), IC5.12 (I0)
unnamed: IC1.2 (O), IC2.2 (I1), IC3.2 (I1), IC4.2 (I1), IC5.2 (I1)
unnamed: IC1.4 (O), IC2.1 (I0), IC2.9 (I0), IC4.1 (I0), IC4.9 (I0)
unnamed: IC2.3 (O), IC2.5 (I1)
unnamed: IC1.6 (O), IC2.4 (I0), IC2.12 (I0), IC3.4 (I0), IC3.12 (I0)
unnamed: IC2.11 (O), OUTPUT.2
unnamed: IC2.8 (O), IC2.13 (I1)
unnamed: IC2.6 (O), OUTPUT.1
unnamed: IC3.3 (O), IC3.5 (I1)
unnamed: IC3.6 (O), OUTPUT.3
unnamed: IC3.8 (O), IC3.13 (I1)
unnamed: IC3.11 (O), OUTPUT.4
unnamed: IC4.3 (O), IC4.5 (I1)
unnamed: IC4.6 (O), OUTPUT.5
unnamed: IC4.8 (O), IC4.13 (I1)
unnamed: IC4.11 (O), OUTPUT.6
unnamed: IC5.3 (O), IC5.5 (I1)
unnamed: IC5.6 (O), OUTPUT.7
unnamed: IC5.8 (O), IC5.13 (I1)
unnamed: IC5.11 (O), OUTPUT.8
VCC: IC1.14 (VCC), IC2.14 (VCC), IC3.14 (VCC), IC4.14 (VCC), IC5.14 (VCC), POWER.1

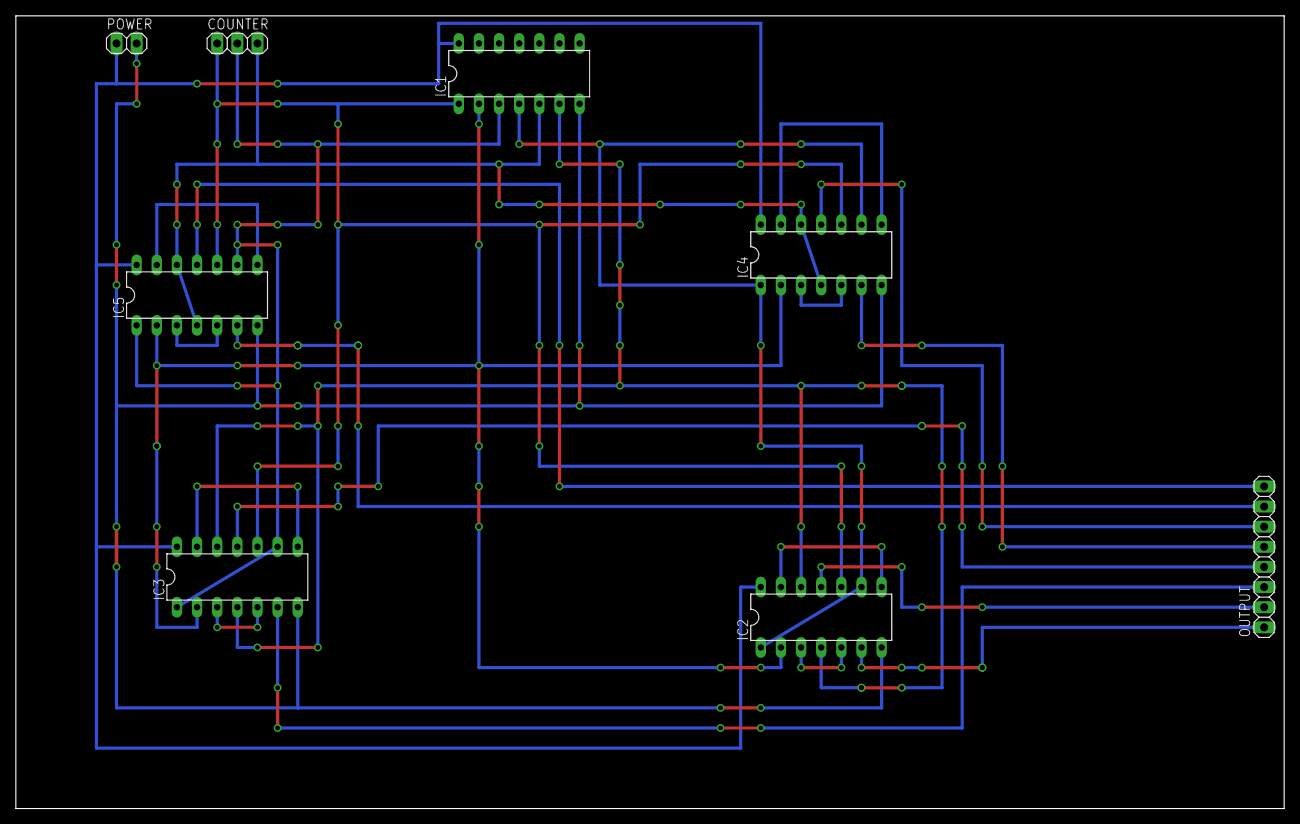
[picture p36: board 3-to-8 Decoder.brd from above]

Board: 2 copper layers, 160.0 x 100.0 mm, 8 parts (0 on the bottom side), 24 nets.
