KPU-RISC/KPU/Eagle/3. Instruction Decoder/01_FETCH_INCREMENT.brd

## EAGLE design Eagle/3. Instruction Decoder/01_FETCH_INCREMENT.brd (2017-04-16)

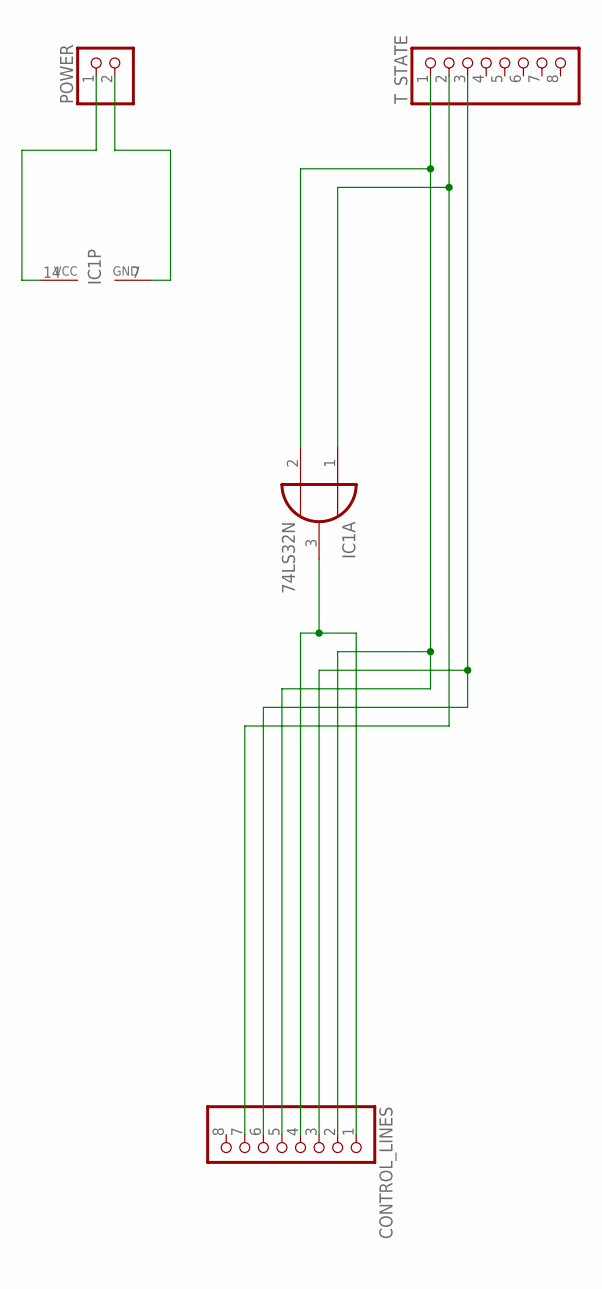
[picture p37: schematic 01_FETCH_INCREMENT.sch]

Parts:
CONTROL_LINES: PINHD-1X8; 1X08
IC1: 74LS32N; DIL14
POWER: PINHD-1X2; 1X02
T_STATE: PINHD-1X8; 1X08

Connections:
GND: IC1.7 (GND), POWER.2
unnamed: CONTROL_LINES.2, CONTROL_LINES.5, IC1.2 (I1), T_STATE.1
unnamed: CONTROL_LINES.7, IC1.1 (I0), T_STATE.2
unnamed: CONTROL_LINES.1, CONTROL_LINES.4, IC1.3 (O)
unnamed: CONTROL_LINES.3, CONTROL_LINES.6, T_STATE.3
VCC: IC1.14 (VCC), POWER.1

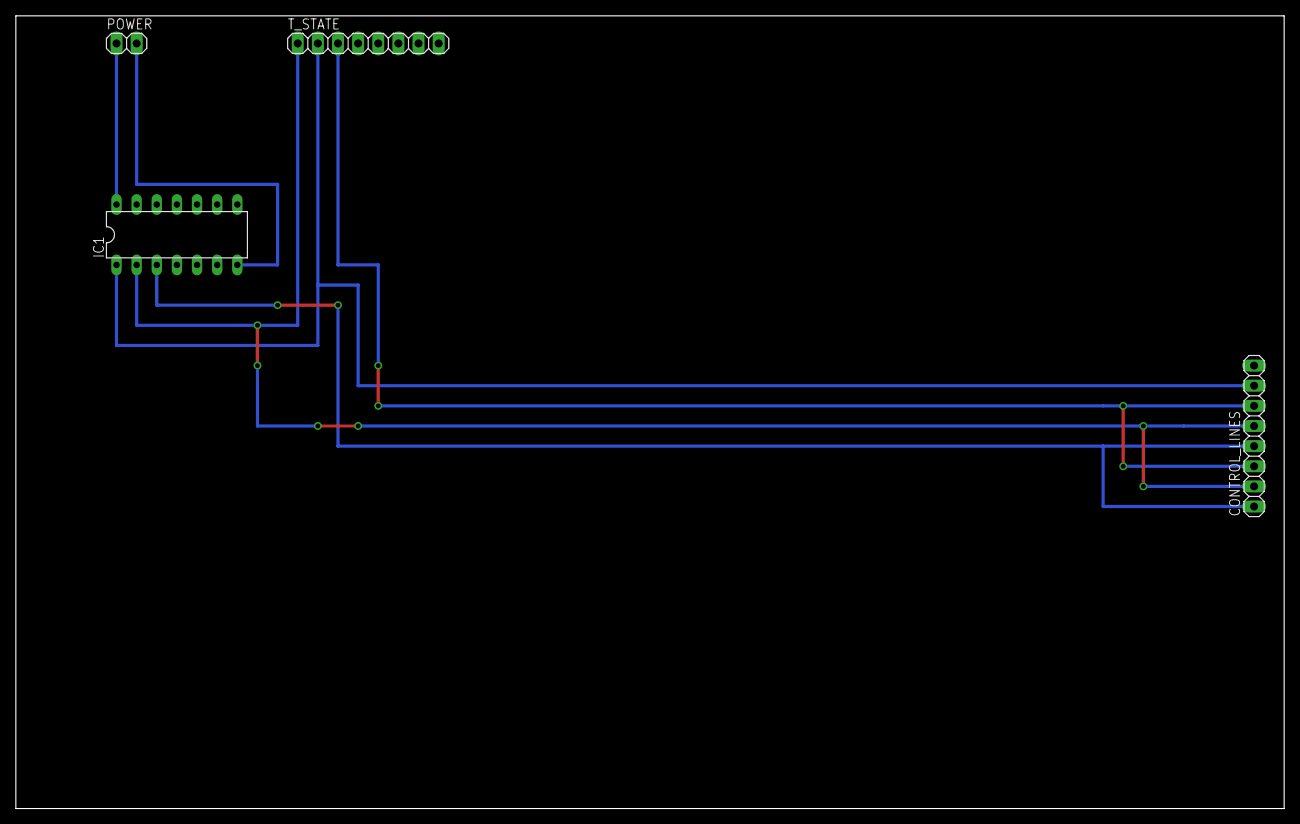
[picture p38: board 01_FETCH_INCREMENT.brd from above]

Board: 2 copper layers, 160.0 x 100.0 mm, 4 parts (0 on the bottom side), 6 nets.
