KPU-RISC/KPU/Eagle/2. ALU/16_FLAGS_Z_S.brd

## EAGLE design Eagle/2. ALU/16_FLAGS_Z_S.brd (2017-04-16)

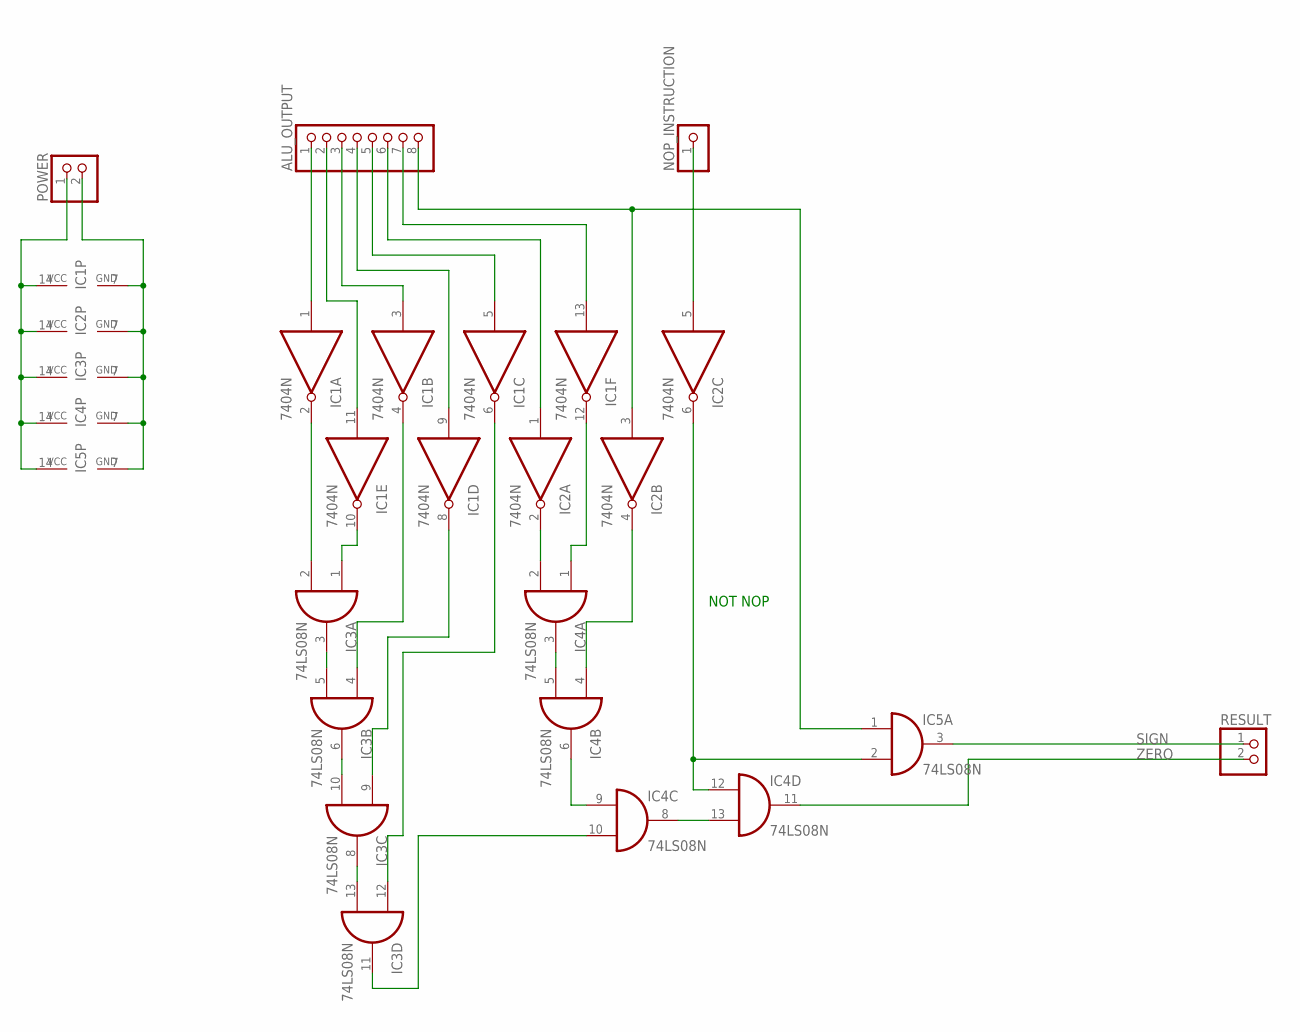
[picture p39: schematic 16_FLAGS_Z_S.sch]

Parts:
ALU_OUTPUT: PINHD-1X8; 1X08
IC1, IC2: 7404N; DIL14
IC3, IC4, IC5: 74LS08N; DIL14
NOP_INSTRUCTION: PINHD-1X1; 1X01
POWER: PINHD-1X2; 1X02
RESULT: PINHD-1X2; 1X02

Connections:
ALU_OUTPUT_1: ALU_OUTPUT.1, IC1.1 (I)
ALU_OUTPUT_2: ALU_OUTPUT.2, IC1.11 (I)
ALU_OUTPUT_3: ALU_OUTPUT.3, IC1.3 (I)
ALU_OUTPUT_4: ALU_OUTPUT.4, IC1.9 (I)
ALU_OUTPUT_5: ALU_OUTPUT.5, IC1.5 (I)
ALU_OUTPUT_6: ALU_OUTPUT.6, IC2.1 (I)
ALU_OUTPUT_7: ALU_OUTPUT.7, IC1.13 (I)
ALU_OUTPUT_8: ALU_OUTPUT.8, IC2.3 (I), IC5.1 (I0)
GND: IC1.7 (GND), IC2.7 (GND), IC3.7 (GND), IC4.7 (GND), IC5.7 (GND), POWER.2
unnamed: IC1.10 (O), IC3.1 (I0)
unnamed: IC1.2 (O), IC3.2 (I1)
unnamed: IC1.4 (O), IC3.4 (I0)
unnamed: IC1.6 (O), IC3.12 (I0)
unnamed: IC1.12 (O), IC4.1 (I0)
unnamed: IC3.3 (O), IC3.5 (I1)
unnamed: IC3.6 (O), IC3.10 (I1)
unnamed: IC1.8 (O), IC3.9 (I0)
unnamed: IC3.8 (O), IC3.13 (I1)
unnamed: IC2.2 (O), IC4.2 (I1)
unnamed: IC4.3 (O), IC4.5 (I1)
unnamed: IC2.4 (O), IC4.4 (I0)
unnamed: IC4.6 (O), IC4.9 (I0)
unnamed: IC3.11 (O), IC4.10 (I1)
unnamed: IC2.6 (O), IC4.12 (I0), IC5.2 (I1)
unnamed: IC4.8 (O), IC4.13 (I1)
NOP_INSTRUCTION: IC2.5 (I), NOP_INSTRUCTION.1
SIGN: IC5.3 (O), RESULT.1
VCC: IC1.14 (VCC), IC2.14 (VCC), IC3.14 (VCC), IC4.14 (VCC), IC5.14 (VCC), POWER.1
ZERO: IC4.11 (O), RESULT.2

Notes on the sheet:
NOT NOP

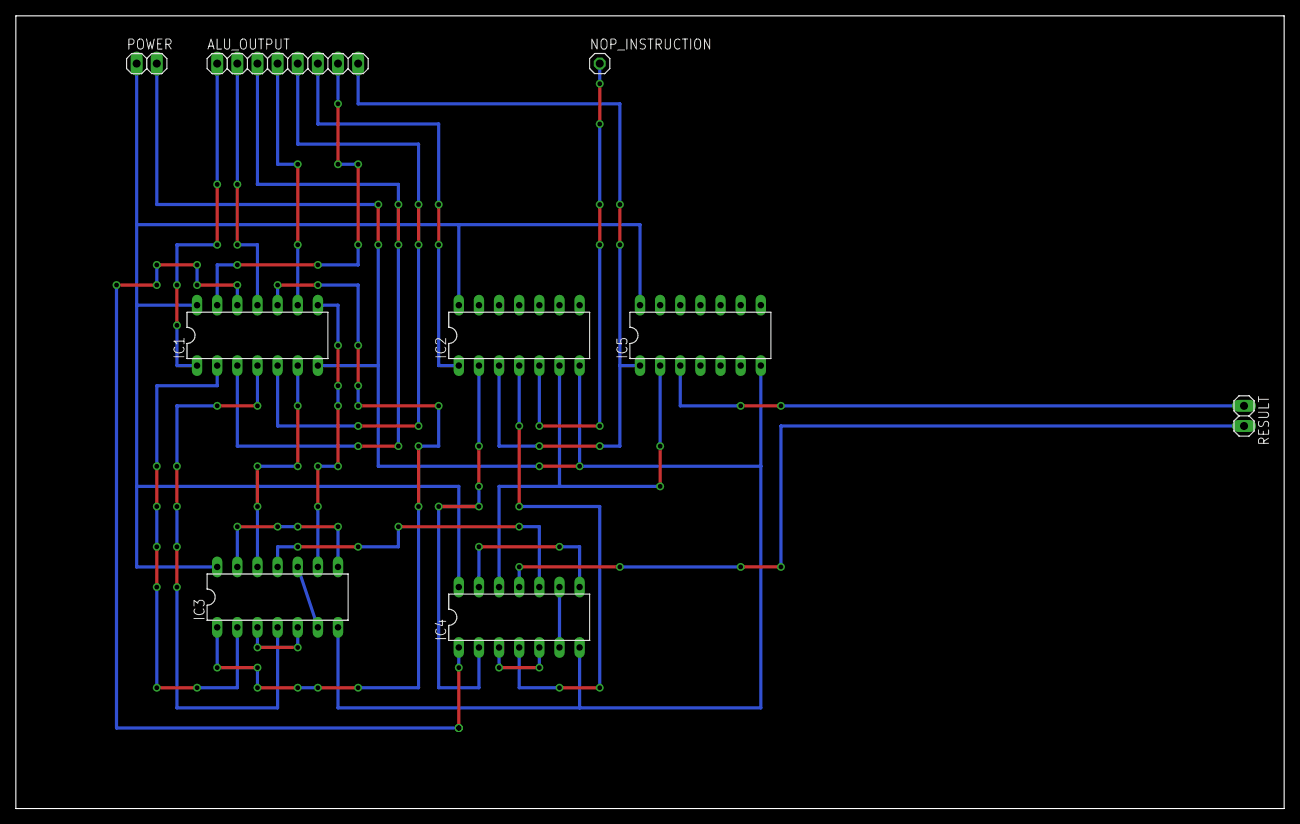
[picture p40: board 16_FLAGS_Z_S.brd from above]

Board: 2 copper layers, 160.0 x 100.0 mm, 9 parts (0 on the bottom side), 29 nets.
