KPU-RISC/KPU/Eagle/3. Instruction Decoder/02_SETAB.brd

## EAGLE design Eagle/3. Instruction Decoder/02_SETAB.brd (2017-04-16)

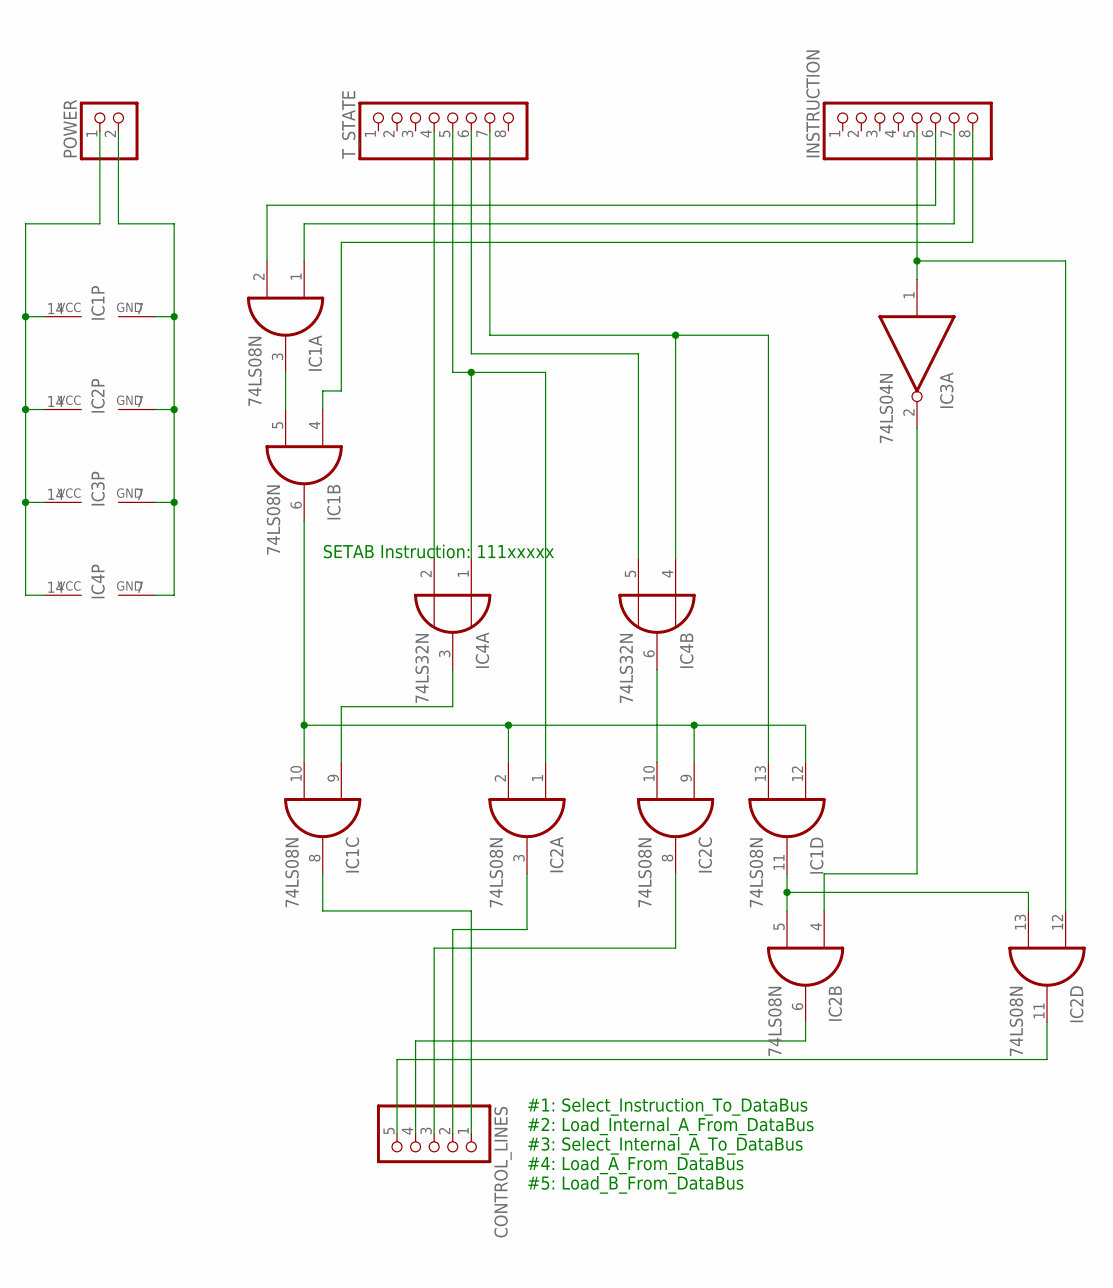
[picture p41: schematic 02_SETAB.sch]

Parts:
CONTROL_LINES: PINHD-1X5; 1X05
IC1, IC2: 74LS08N; DIL14
IC3: 74LS04N; DIL14
IC4: 74LS32N; DIL14
INSTRUCTION: PINHD-1X8; 1X08
POWER: PINHD-1X2; 1X02
T_STATE: PINHD-1X8; 1X08

Connections:
GND: IC1.7 (GND), IC2.7 (GND), IC3.7 (GND), IC4.7 (GND), POWER.2
unnamed: IC1.2 (I1), INSTRUCTION.6
unnamed: IC1.1 (I0), INSTRUCTION.7
unnamed: IC1.3 (O), IC1.5 (I1)
unnamed: IC1.4 (I0), INSTRUCTION.8
unnamed: IC2.1 (I0), IC4.1 (I0), T_STATE.5
unnamed: IC4.2 (I1), T_STATE.4
unnamed: CONTROL_LINES.1, IC1.8 (O)
unnamed: IC1.6 (O), IC1.10 (I1), IC1.12 (I0), IC2.2 (I1), IC2.9 (I0)
unnamed: IC1.9 (I0), IC4.3 (O)
unnamed: CONTROL_LINES.4, IC2.6 (O)
unnamed: IC2.12 (I0), IC3.1 (I), INSTRUCTION.5
unnamed: IC2.4 (I0), IC3.2 (O)
unnamed: CONTROL_LINES.2, IC2.3 (O)
unnamed: IC4.5 (I1), T_STATE.6
unnamed: IC1.13 (I1), IC4.4 (I0), T_STATE.7
unnamed: IC2.10 (I1), IC4.6 (O)
unnamed: CONTROL_LINES.3, IC2.8 (O)
unnamed: IC1.11 (O), IC2.5 (I1), IC2.13 (I1)
unnamed: CONTROL_LINES.5, IC2.11 (O)
VCC: IC1.14 (VCC), IC2.14 (VCC), IC3.14 (VCC), IC4.14 (VCC), POWER.1

Notes on the sheet:
SETAB Instruction: 111xxxxx
#1: Select_Instruction_To_DataBus #2: Load_Internal_A_From_DataBus #3: Select_Internal_A_To_DataBus #4: Load_A_From_DataBus #5: Load_B_From_DataBus

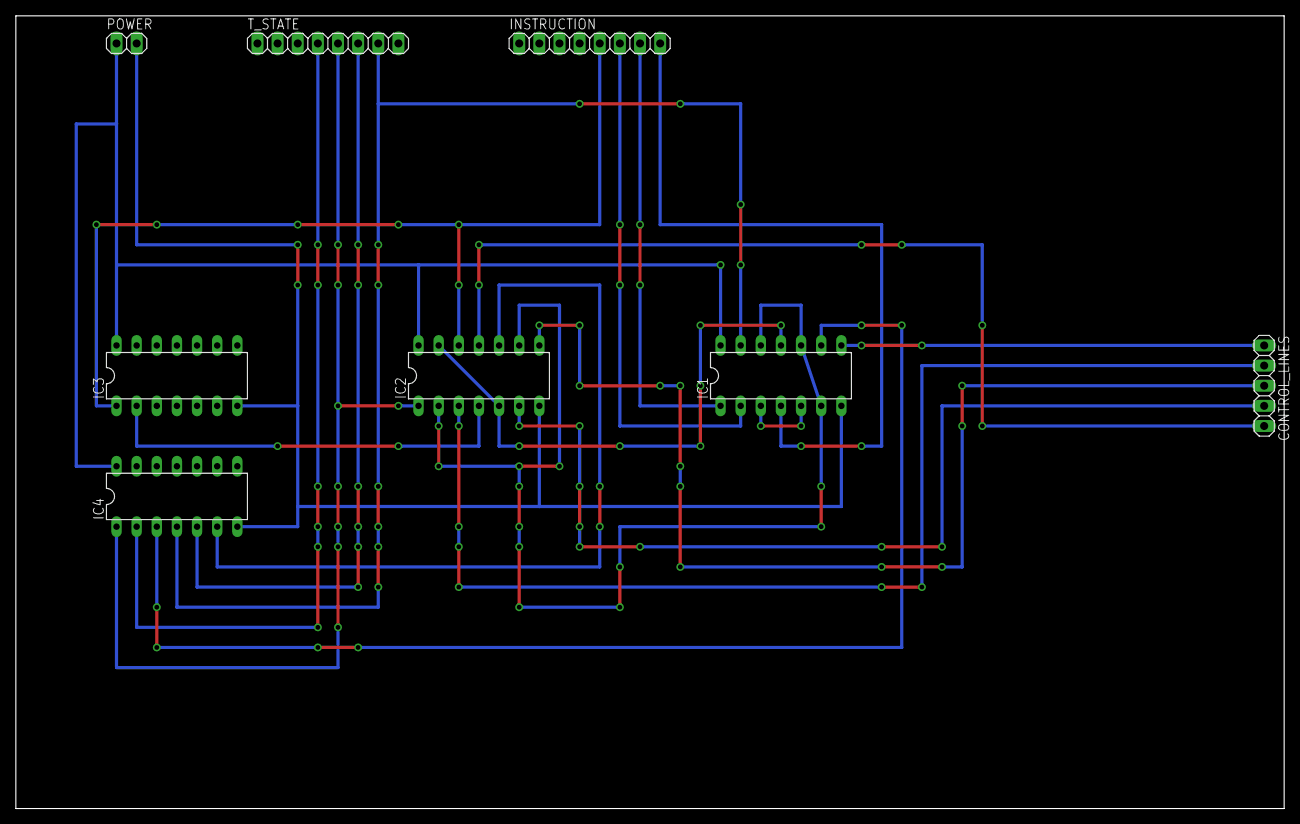
[picture p42: board 02_SETAB.brd from above]

Board: 2 copper layers, 160.0 x 100.0 mm, 8 parts (0 on the bottom side), 21 nets.
