KPU-RISC/KPU/Eagle/4. Register/16-Bit Register.brd

## EAGLE design Eagle/4. Register/16-Bit Register.brd (2017-04-16)

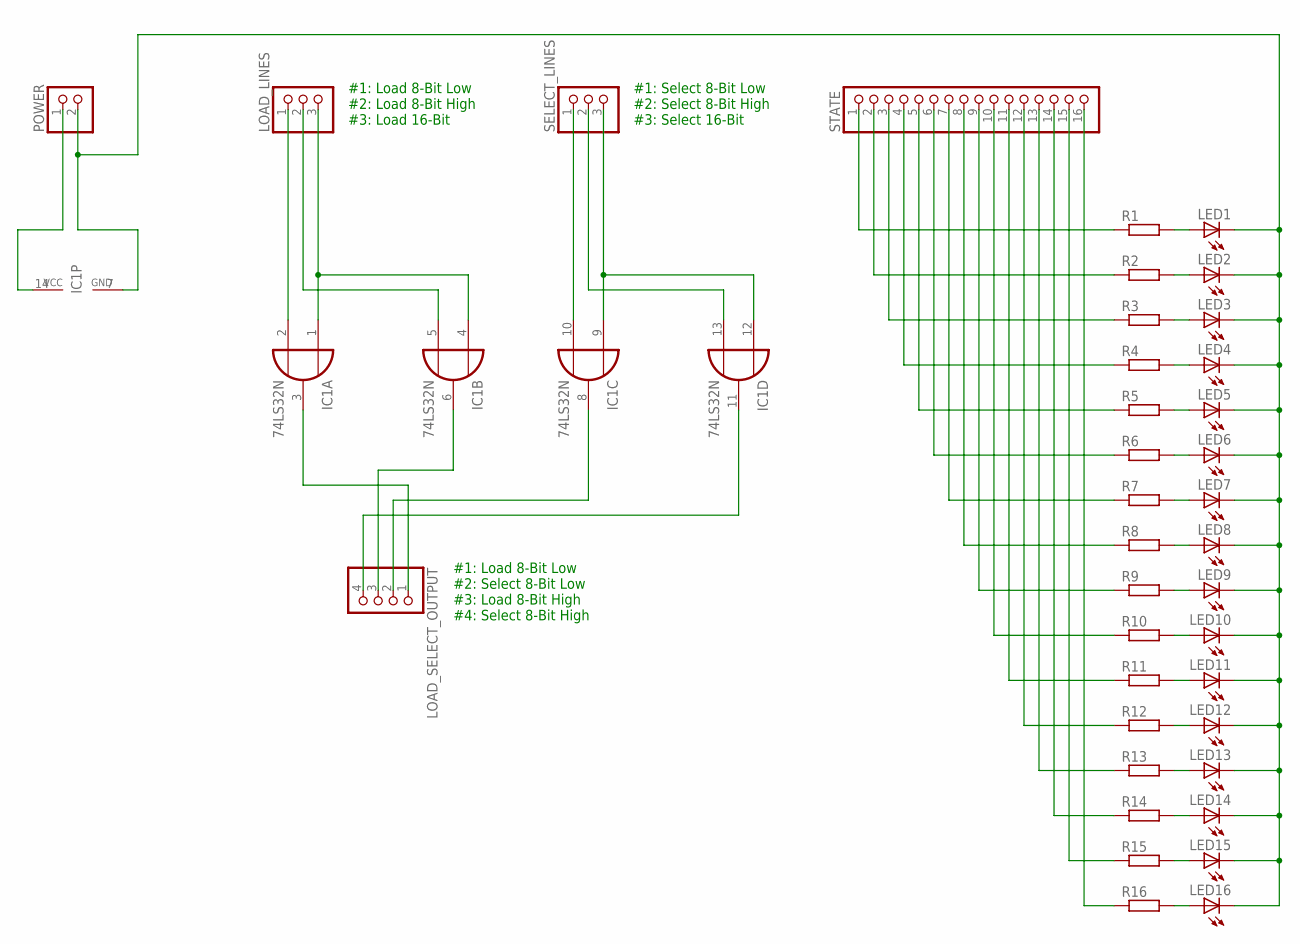
[picture p43: schematic 16-Bit Register.sch]

Parts:
IC1: 74LS32N; DIL14
LED1, LED2, LED3, LED4, LED5, LED6, LED7, LED8, LED9, LED10, LED11, LED12, LED13, LED14, LED15, LED16: LED3MM
LOAD_LINES: PINHD-1X3; 1X03
LOAD_SELECT_OUTPUT: PINHD-1X4; 1X04
POWER: PINHD-1X2; 1X02
R1, R2, R3, R4, R5, R6, R7, R8, R9, R10, R11, R12, R13, R14, R15, R16: R-EU_0207/7; 0207/7
SELECT_LINES: PINHD-1X3; 1X03
STATE: PINHD-1X16; 1X16

Connections:
GND: IC1.7 (GND), LED1.K (C), LED2.K (C), LED3.K (C), LED4.K (C), LED5.K (C), LED6.K (C), LED7.K (C), LED8.K (C), LED9.K (C), LED10.K (C), LED11.K (C), LED12.K (C), LED13.K (C), LED14.K (C), LED15.K (C), LED16.K (C), POWER.2
unnamed: IC1.2 (I1), LOAD_LINES.1
unnamed: IC1.1 (I0), IC1.4 (I0), LOAD_LINES.3
unnamed: IC1.5 (I1), LOAD_LINES.2
unnamed: IC1.10 (I1), SELECT_LINES.1
unnamed: IC1.9 (I0), IC1.12 (I0), SELECT_LINES.3
unnamed: IC1.13 (I1), SELECT_LINES.2
unnamed: IC1.3 (O), LOAD_SELECT_OUTPUT.1
unnamed: IC1.6 (O), LOAD_SELECT_OUTPUT.3
unnamed: IC1.8 (O), LOAD_SELECT_OUTPUT.2
unnamed: IC1.11 (O), LOAD_SELECT_OUTPUT.4
unnamed: R1.1, STATE.1
unnamed: R2.1, STATE.2
unnamed: R3.1, STATE.3
unnamed: R4.1, STATE.4
unnamed: R5.1, STATE.5
unnamed: R6.1, STATE.6
unnamed: R7.1, STATE.7
unnamed: R8.1, STATE.8
unnamed: R9.1, STATE.9
unnamed: R10.1, STATE.10
unnamed: R11.1, STATE.11
unnamed: R12.1, STATE.12
unnamed: R13.1, STATE.13
unnamed: R14.1, STATE.14
unnamed: R15.1, STATE.15
unnamed: R16.1, STATE.16
unnamed: LED16.A, R16.2
unnamed: LED15.A, R15.2
unnamed: LED14.A, R14.2
unnamed: LED13.A, R13.2
unnamed: LED12.A, R12.2
unnamed: LED11.A, R11.2
unnamed: LED10.A, R10.2
unnamed: LED9.A, R9.2
unnamed: LED8.A, R8.2
unnamed: LED7.A, R7.2
unnamed: LED6.A, R6.2
unnamed: LED5.A, R5.2
unnamed: LED4.A, R4.2
unnamed: LED3.A, R3.2
unnamed: LED2.A, R2.2
unnamed: LED1.A, R1.2
VCC: IC1.14 (VCC), POWER.1

Notes on the sheet:
#1: Load 8-Bit Low #2: Load 8-Bit High #3: Load 16-Bit
#1: Select 8-Bit Low #2: Select 8-Bit High #3: Select 16-Bit
#1: Load 8-Bit Low #2: Select 8-Bit Low #3: Load 8-Bit High #4: Select 8-Bit High

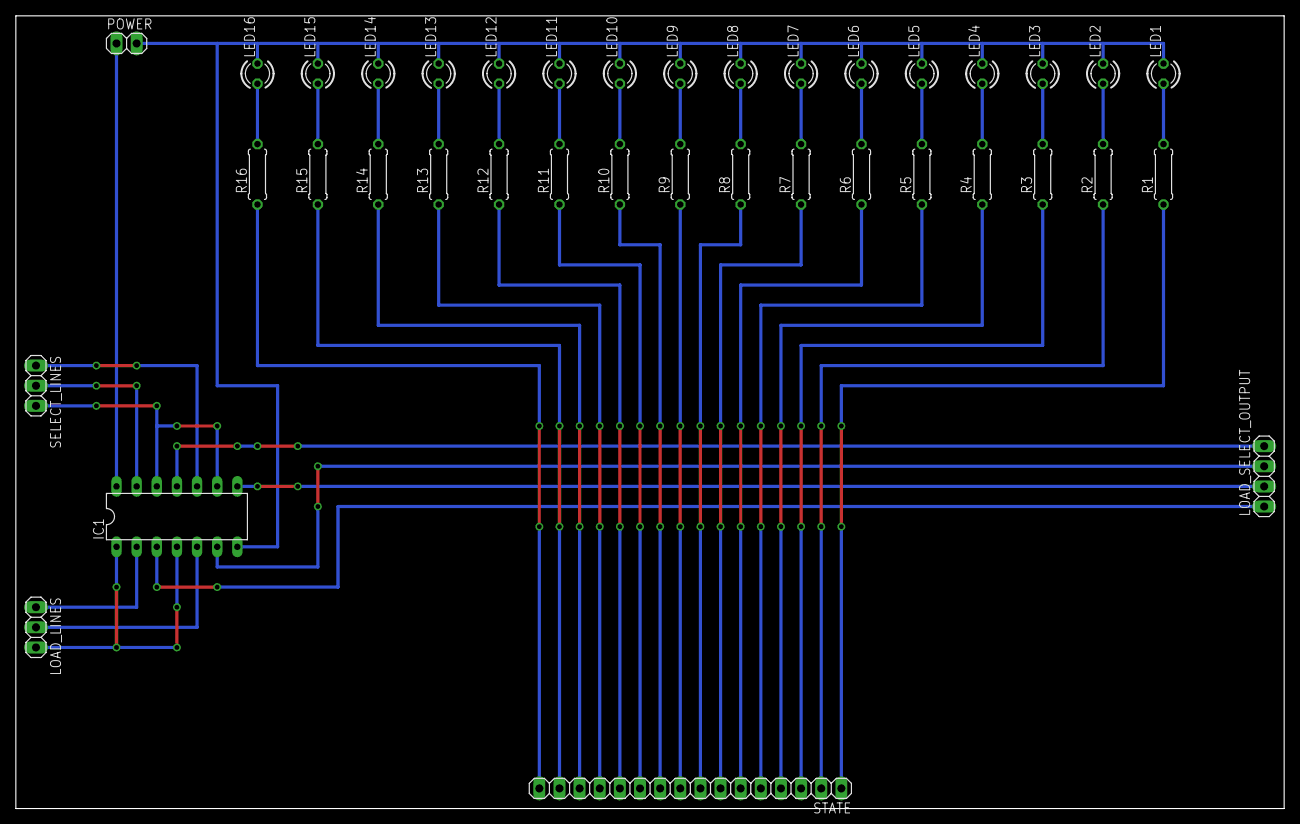
[picture p44: board 16-Bit Register.brd from above]

Board: 2 copper layers, 160.0 x 100.0 mm, 38 parts (0 on the bottom side), 44 nets.
